Apiquet/STI_Robotic_Competition_Mechanics/AxialBlock.SLDPRT

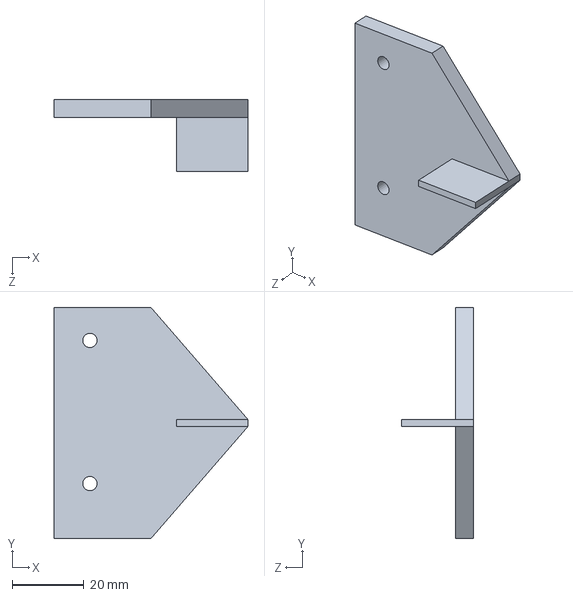
[picture p20: CAD file, 2019-05-12]
AxialBlock.SLDPRT
54.1 x 64.5 x 20.0 mm
