Apiquet/STI_Robotic_Competition_Mechanics/Cam_support/front_cam/Camera_Case.SLDPRT

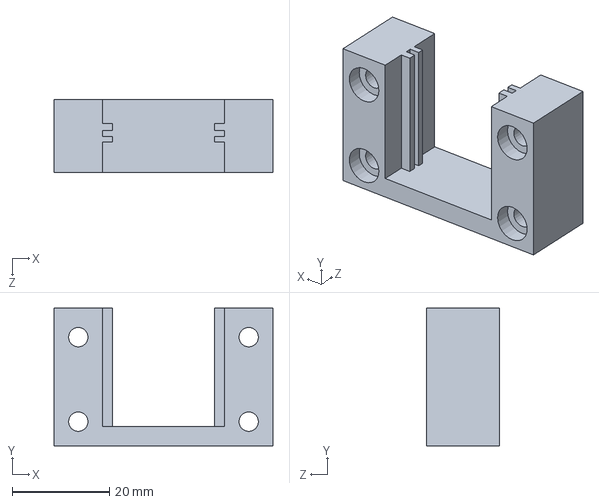
[picture p21: CAD file, 2019-05-05]
Cam_support/front_cam/Camera_Case.SLDPRT
45.1 x 28.4 x 15.0 mm
