Apiquet/STI_Robotic_Competition_Mechanics/Collector_Mechanism/Top_Roller_Holder.SLDPRT

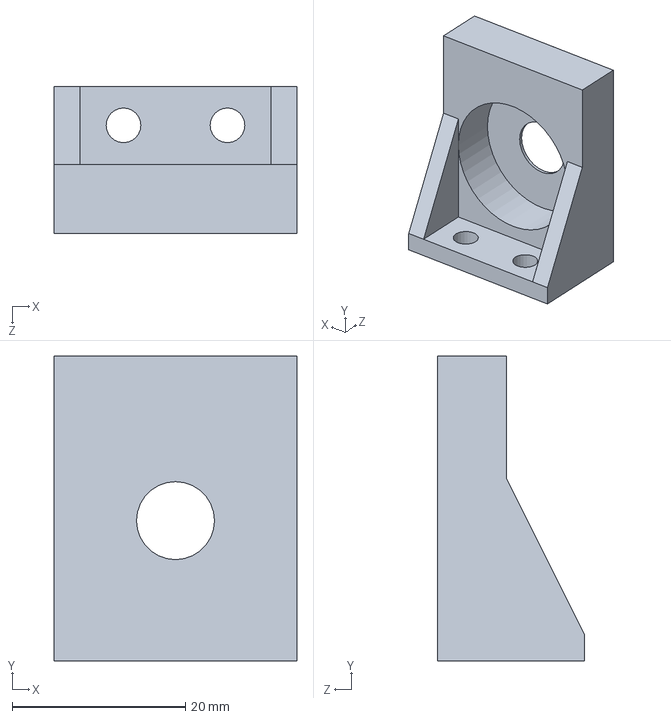
[picture p22: CAD file, 2019-06-13]
Collector_Mechanism/Top_Roller_Holder.SLDPRT
28.0 x 35.2 x 17.0 mm
