Apiquet/STI_Robotic_Competition_Mechanics/Divers/electronics_board/SHARP Sensor.STEP

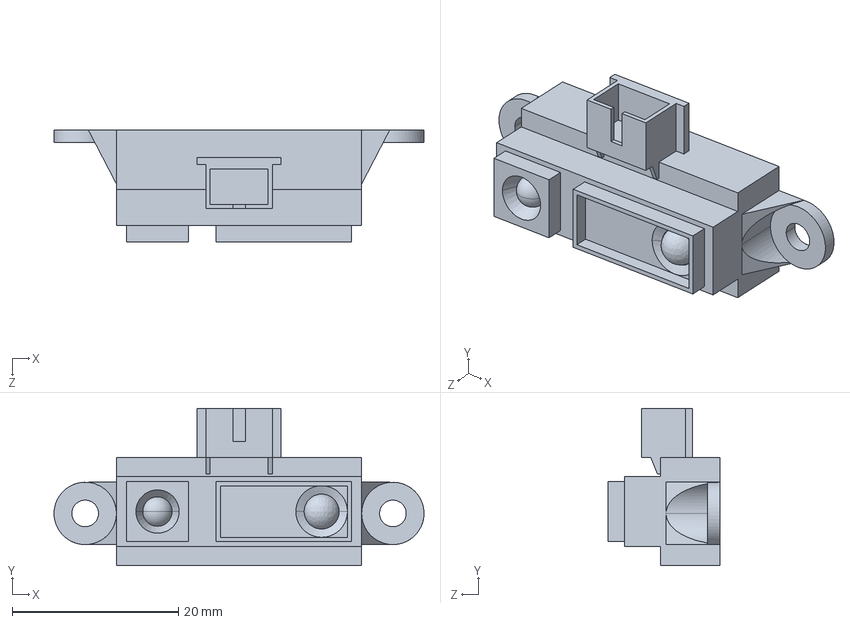
[picture p23: CAD file, 2019-05-03]
Divers/electronics_board/SHARP Sensor.STEP
44.5 x 18.9 x 13.5 mm
