Apiquet/STI_Robotic_Competition_Mechanics/Divers/motors/re25.SLDPRT

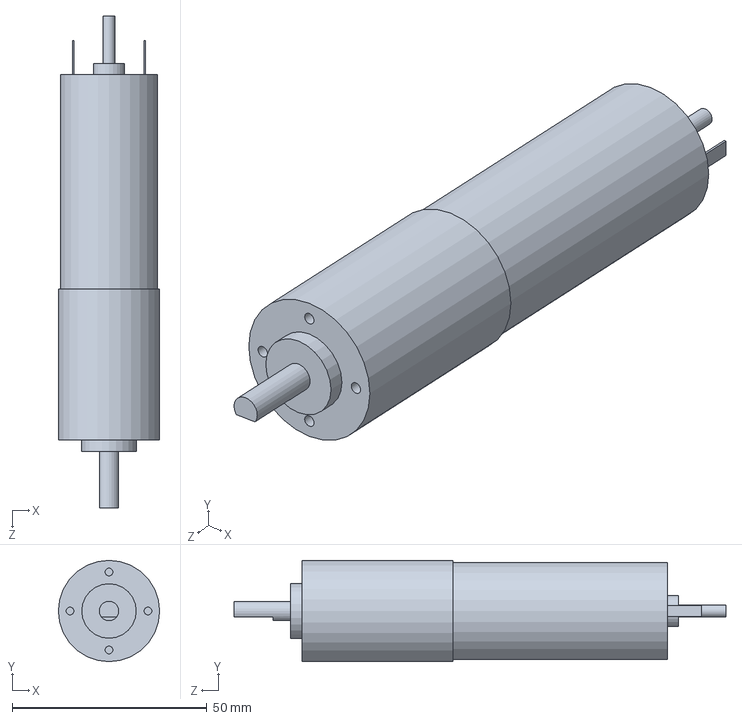
[picture p24: CAD file, 2019-06-13]
Divers/motors/re25.SLDPRT
26.0 x 26.0 x 126.2 mm
