Apiquet/STI_Robotic_Competition_Mechanics/Field/Ramp_True.SLDPRT

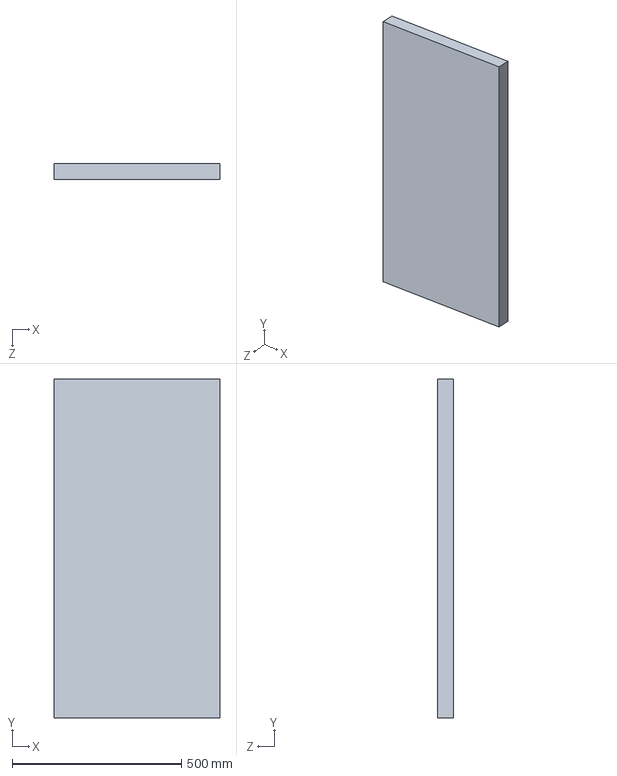
[picture p25: CAD file, 2019-05-09]
Field/Ramp_True.SLDPRT
490.0 x 1001.0 x 47.5 mm
