Apiquet/STI_Robotic_Competition_Mechanics/Prototype_Bottle_Mechanism/high_roller_left_support.SLDPRT

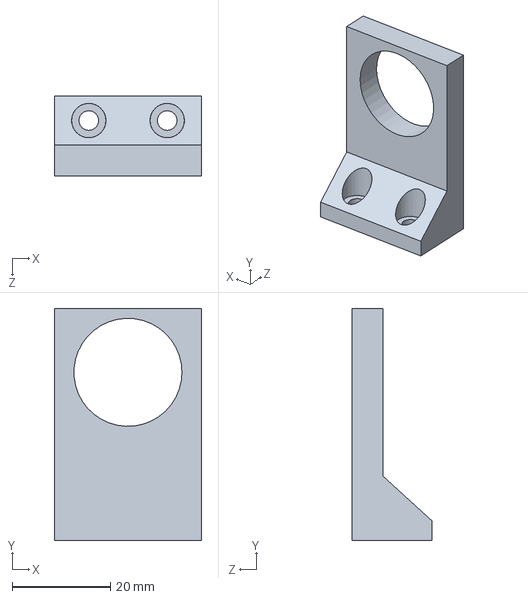
[picture p26: CAD file, 2019-03-28]
Prototype_Bottle_Mechanism/high_roller_left_support.SLDPRT
30.0 x 47.3 x 16.3 mm
