Apiquet/STI_Robotic_Competition_Mechanics/Cam_support/V2/Cone.SLDPRT

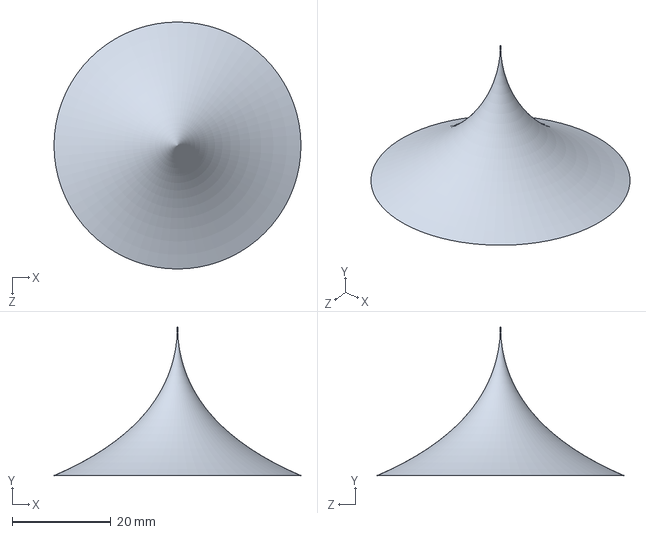
[picture p27: CAD file, 2019-06-13]
Cam_support/V2/Cone.SLDPRT
50.0 x 30.0 x 50.0 mm
