Apiquet/STI_Robotic_Competition_Mechanics/Collector_Mechanism/Bottom_Right_Roller_Holder.SLDPRT

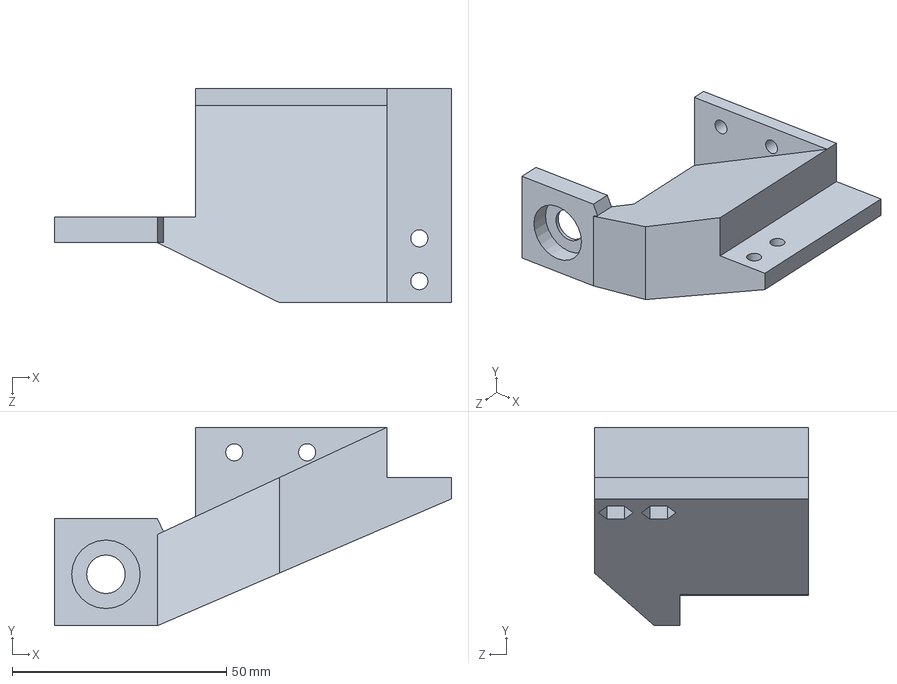
[picture p28: CAD file, 2019-06-13]
Collector_Mechanism/Bottom_Right_Roller_Holder.SLDPRT
92.6 x 46.3 x 50.0 mm
