Apiquet/STI_Robotic_Competition_Mechanics/Divers/electronics_board/DC8-40V_DC12V.SLDPRT

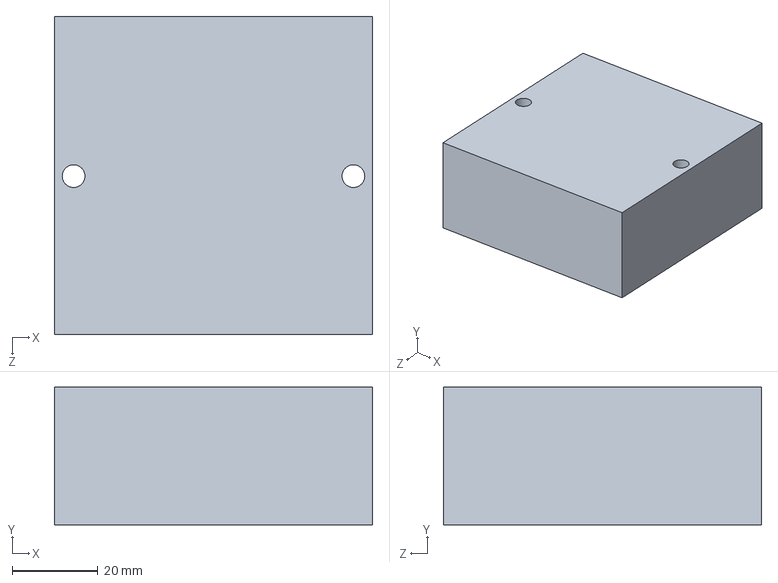
[picture p29: CAD file, 2019-04-24]
Divers/electronics_board/DC8-40V_DC12V.SLDPRT
74.0 x 32.0 x 74.0 mm
