Apiquet/STI_Robotic_Competition_Mechanics/Divers/motors/H38S.SLDPRT

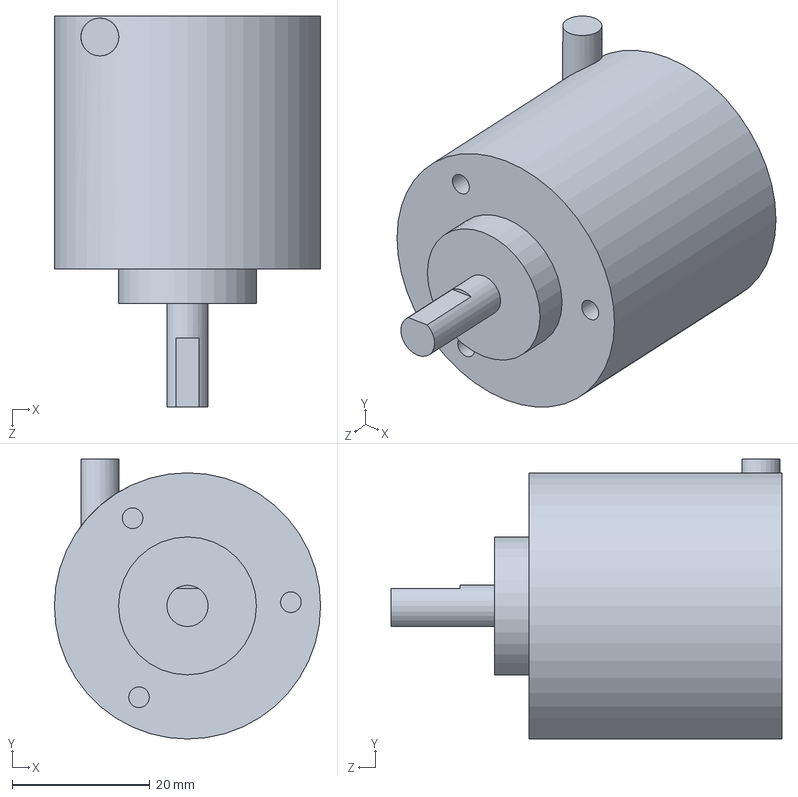
[picture p30: CAD file, 2019-04-23]
Divers/motors/H38S.SLDPRT
38.6 x 40.6 x 56.7 mm
