Apiquet/STI_Robotic_Competition_Mechanics/Divers/Panel_Right.SLDPRT

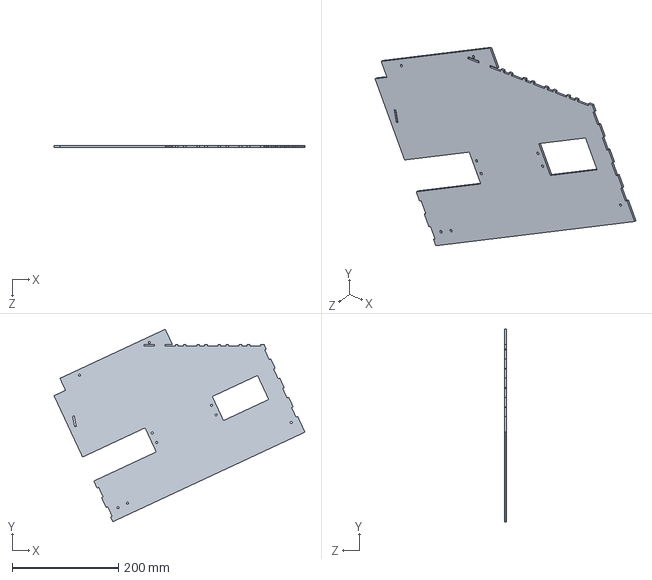
[picture p31: CAD file, 2019-06-15]
Divers/Panel_Right.SLDPRT
473.3 x 363.1 x 3.30 mm
