Apiquet/STI_Robotic_Competition_Mechanics/Drive_Base/Encodeur_Wheel.SLDPRT

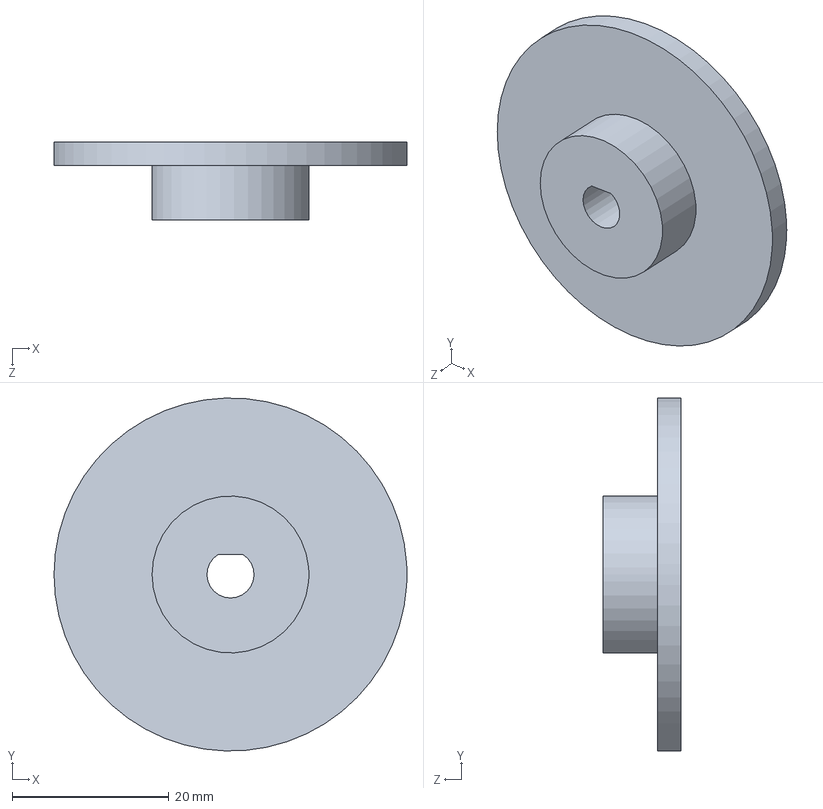
[picture p32: CAD file, 2019-06-13]
Drive_Base/Encodeur_Wheel.SLDPRT
45.0 x 45.0 x 10.0 mm
