Apiquet/STI_Robotic_Competition_Mechanics/Field/Real_Ramp.SLDPRT

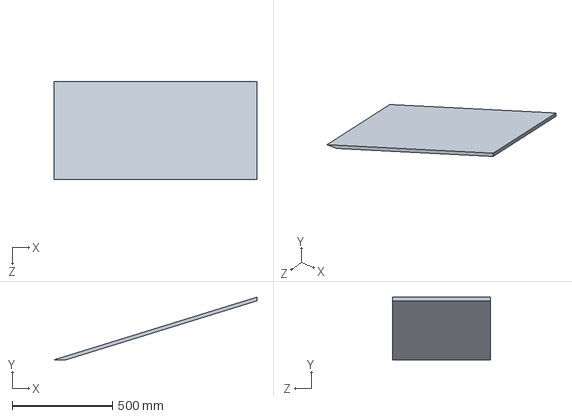
[picture p33: CAD file, 2019-05-09]
Field/Real_Ramp.SLDPRT
1013.0 x 313.0 x 490.0 mm
