Apiquet/STI_Robotic_Competition_Mechanics/Prototype_Bottle_Mechanism/left_motor_support.SLDPRT

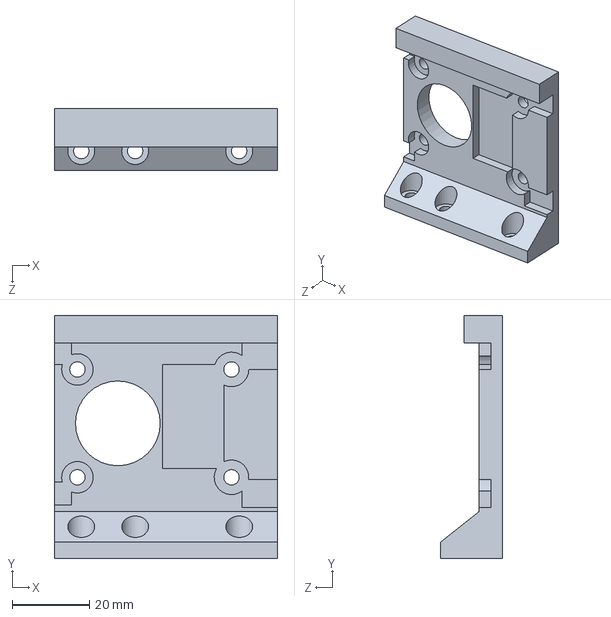
[picture p34: CAD file, 2019-03-28]
Prototype_Bottle_Mechanism/left_motor_support.SLDPRT
58.0 x 63.1 x 16.0 mm
