Apiquet/STI_Robotic_Competition_Mechanics/Sensor/side_sensor_holder.sldprt

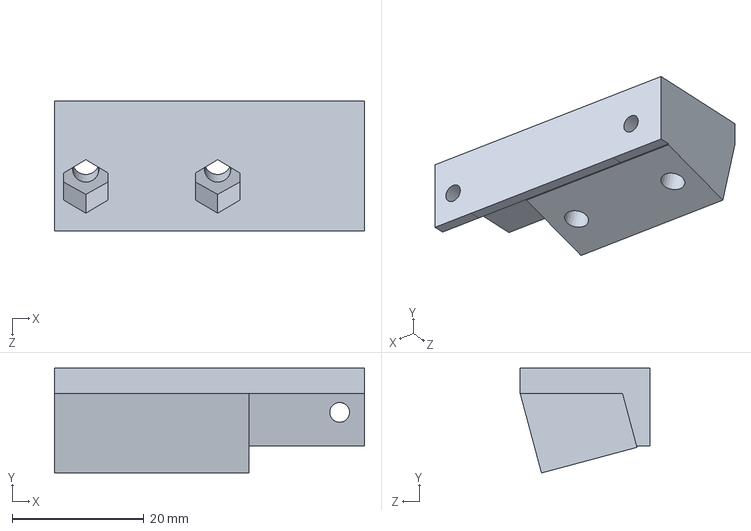
[picture p35: CAD file, 2019-06-13]
Sensor/side_sensor_holder.sldprt
47.0 x 15.9 x 19.7 mm
