Apiquet/STI_Robotic_Competition_Mechanics/Cam_support/V2/Camera_Support.SLDPRT

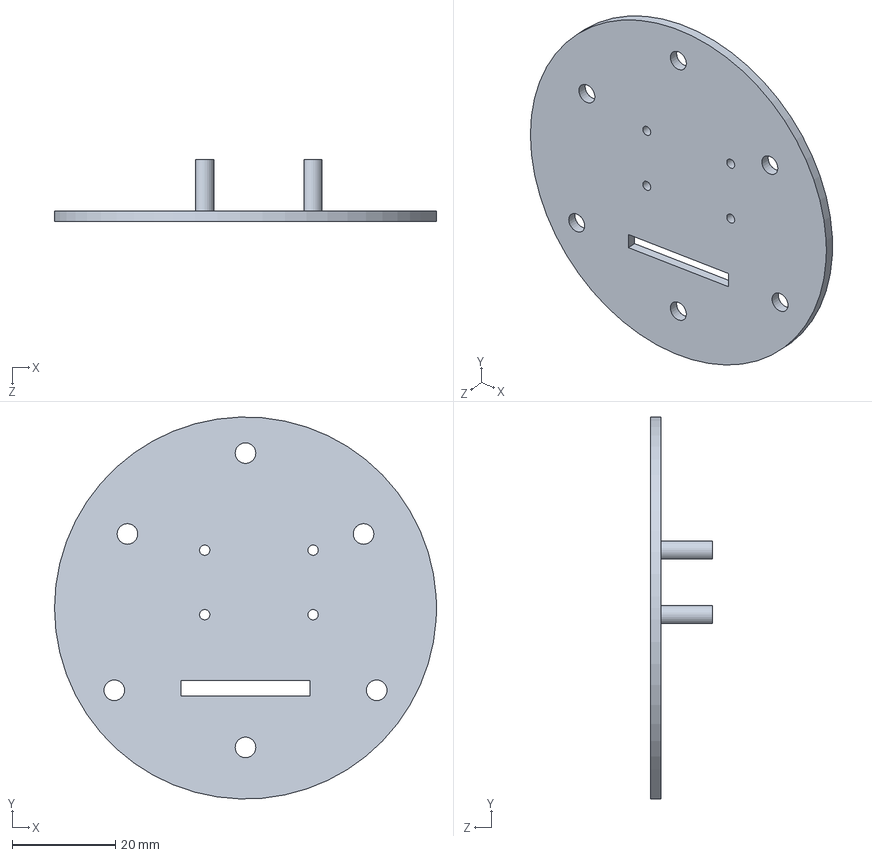
[picture p36: CAD file, 2019-06-13]
Cam_support/V2/Camera_Support.SLDPRT
74.0 x 74.0 x 12.0 mm
