Apiquet/STI_Robotic_Competition_Mechanics/Divers/electronics_board/2x15A_lite.SLDPRT

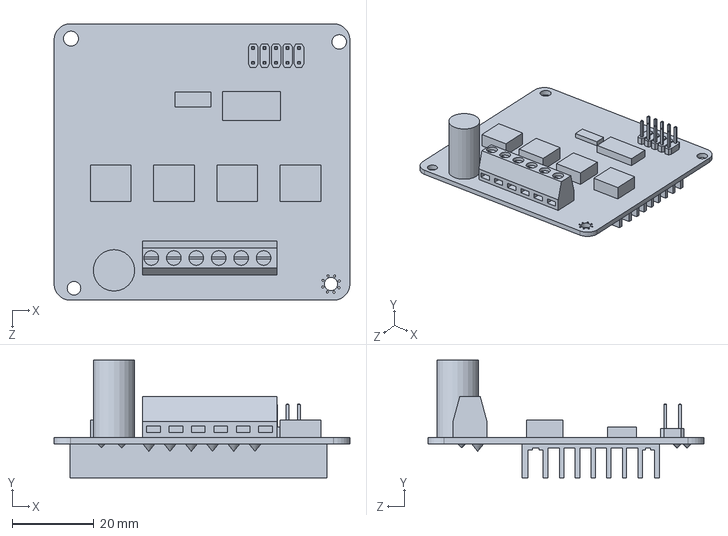
[picture p37: CAD file, 2019-04-24]
Divers/electronics_board/2x15A_lite.SLDPRT
72.5 x 28.9 x 67.7 mm
