Apiquet/STI_Robotic_Competition_Mechanics/Divers/Mirror_Corner_Bearing_Holder.sldprt

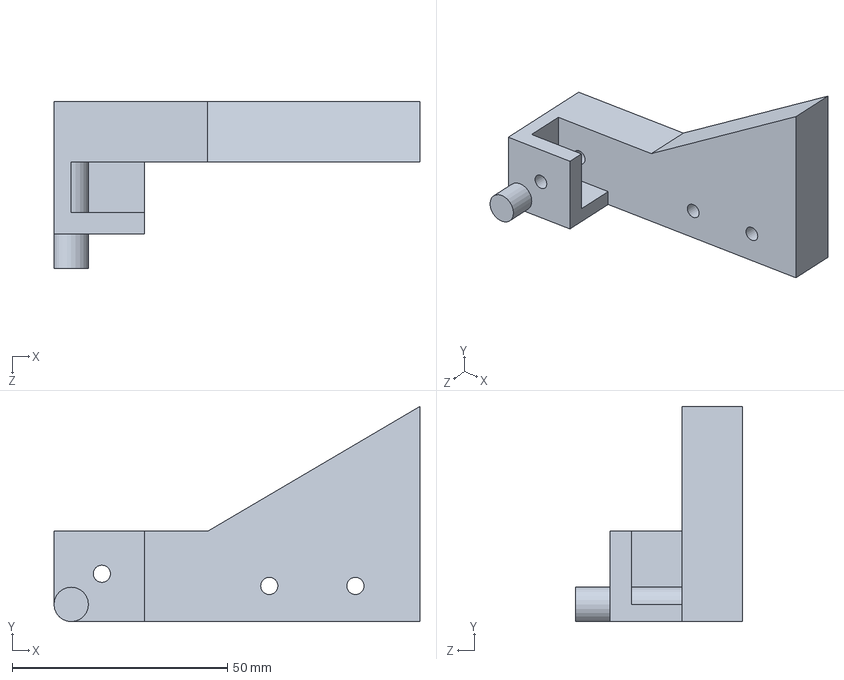
[picture p38: CAD file, 2019-06-13]
Divers/Mirror_Corner_Bearing_Holder.sldprt
85.0 x 50.0 x 38.7 mm
