Apiquet/STI_Robotic_Competition_Mechanics/Field/Obstacle.SLDPRT

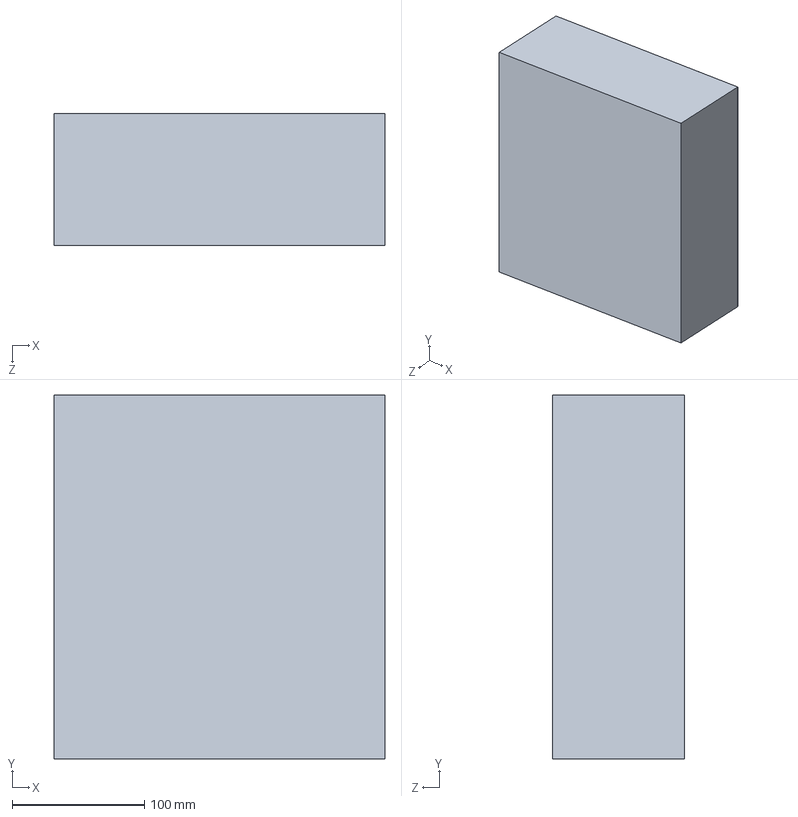
[picture p39: CAD file, 2019-05-03]
Field/Obstacle.SLDPRT
250.0 x 275.0 x 100.0 mm
