Apiquet/STI_Robotic_Competition_Mechanics/Prototype_Bottle_Mechanism/big_motor_supportv2.SLDPRT

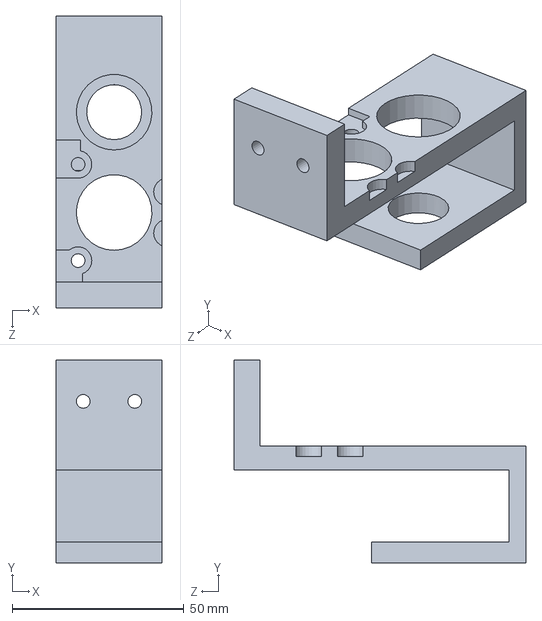
[picture p40: CAD file, 2019-03-20]
Prototype_Bottle_Mechanism/big_motor_supportv2.SLDPRT
31.0 x 59.0 x 85.0 mm
