Apiquet/STI_Robotic_Competition_Mechanics/Sensor/Sensor_Side_Back_V2.sldprt

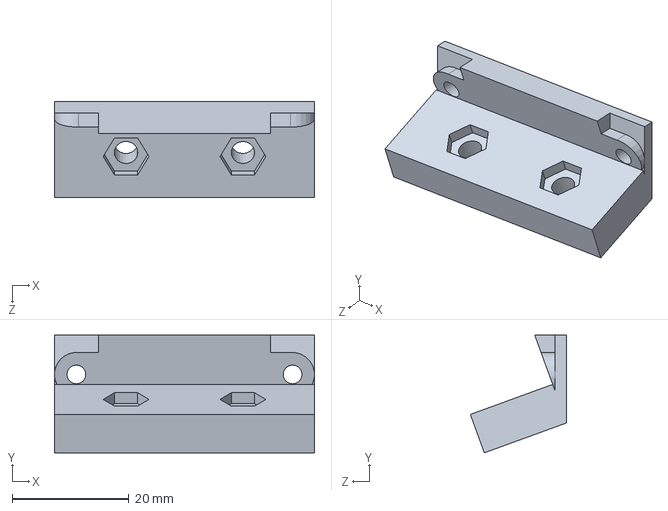
[picture p41: CAD file, 2019-05-20]
Sensor/Sensor_Side_Back_V2.sldprt
44.5 x 20.1 x 16.5 mm
