Apiquet/STI_Robotic_Competition_Mechanics/Cam_support/V2/base_cam_support.SLDPRT

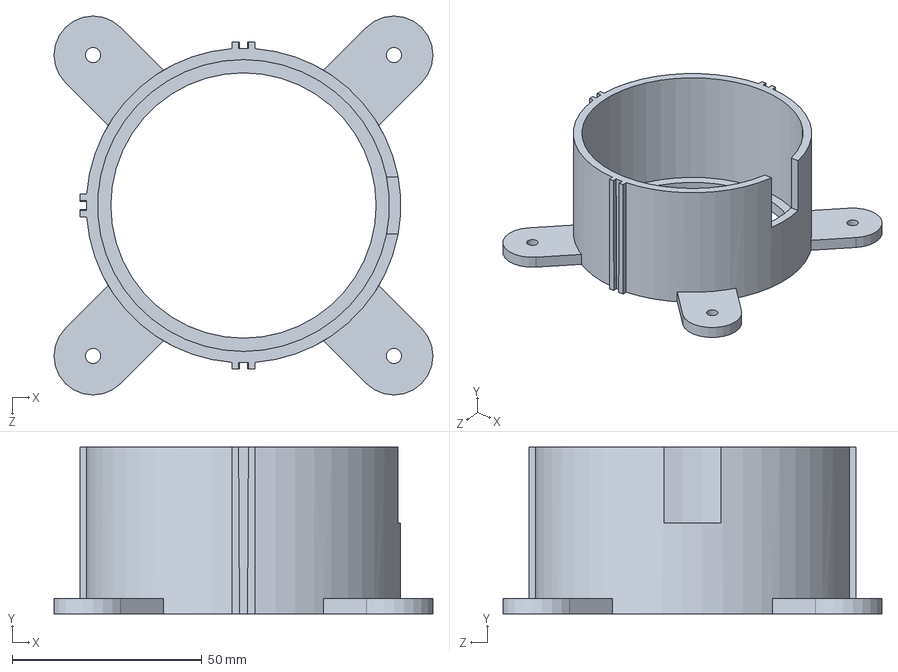
[picture p42: CAD file, 2019-06-13]
Cam_support/V2/base_cam_support.SLDPRT
100.0 x 44.0 x 100.0 mm
