Apiquet/STI_Robotic_Competition_Mechanics/Collector_Mechanism/Back_Motor_Roller_Support.SLDPRT

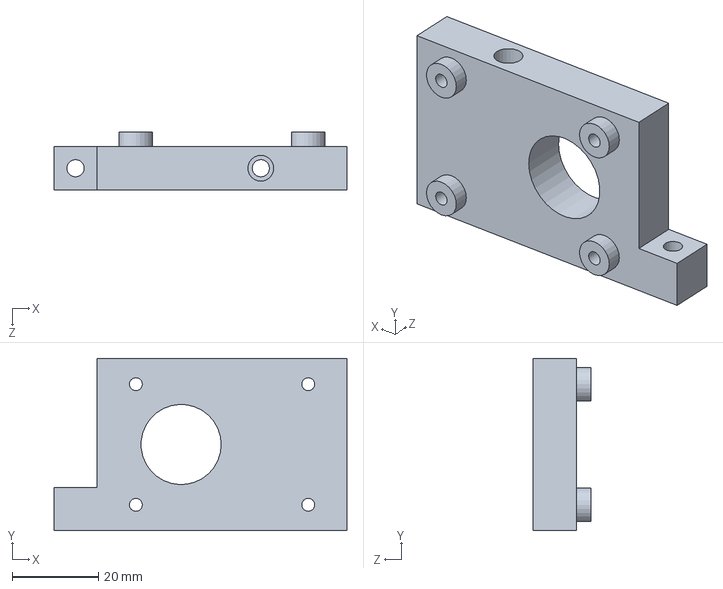
[picture p43: CAD file, 2019-05-30]
Collector_Mechanism/Back_Motor_Roller_Support.SLDPRT
68.0 x 40.0 x 13.4 mm
