Apiquet/STI_Robotic_Competition_Mechanics/Divers/electronics_board/powerboard_robopoly.SLDPRT

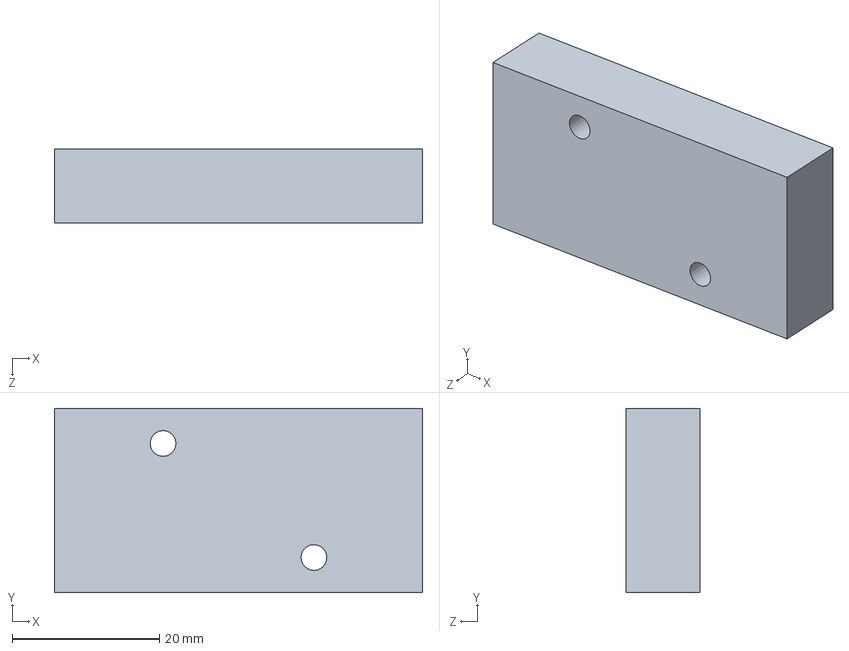
[picture p44: CAD file, 2019-03-14]
Divers/electronics_board/powerboard_robopoly.SLDPRT
50.0 x 25.0 x 10.0 mm
