Apiquet/STI_Robotic_Competition_Mechanics/Divers/Panel_Roof.SLDPRT

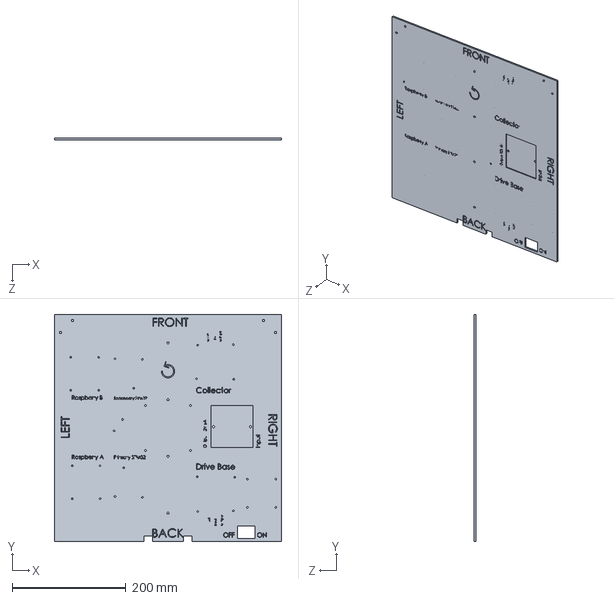
[picture p45: CAD file, 2019-06-13]
Divers/Panel_Roof.SLDPRT
400.0 x 400.0 x 3.30 mm
