Apiquet/STI_Robotic_Competition_Mechanics/Prototype_Bottle_Mechanism/wedge_left_side.SLDPRT

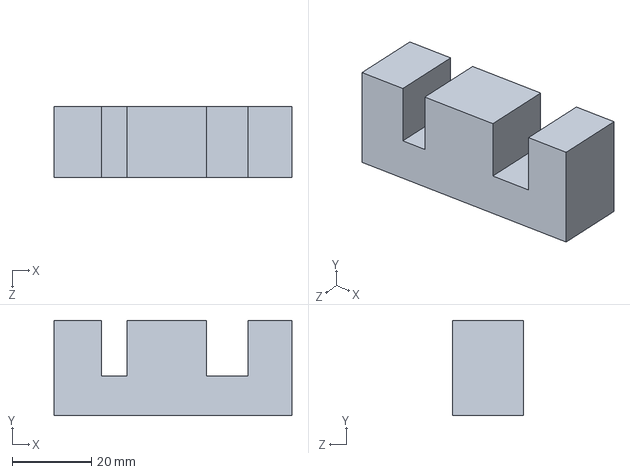
[picture p46: CAD file, 2019-03-18]
Prototype_Bottle_Mechanism/wedge_left_side.SLDPRT
60.0 x 24.0 x 18.0 mm
