Apiquet/STI_Robotic_Competition_Mechanics/Sensor/Front_Sensor_holder.SLDPRT

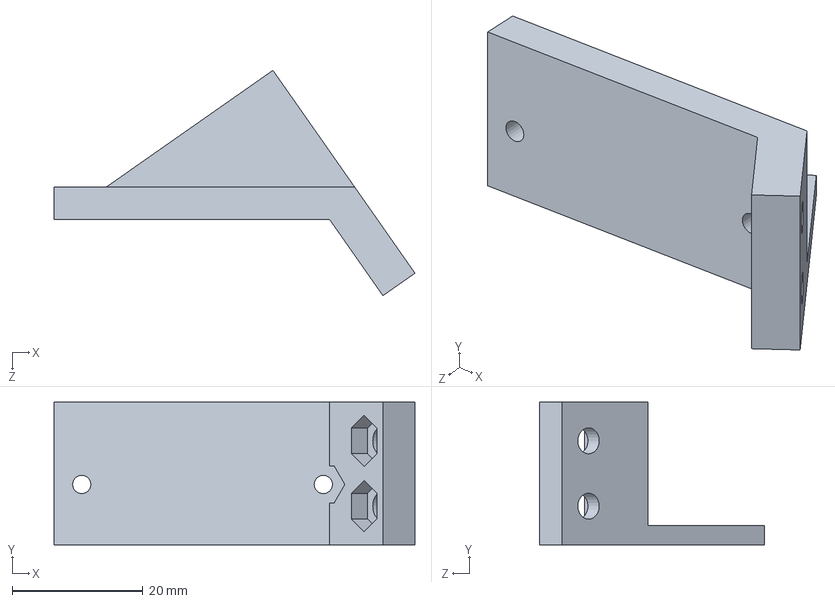
[picture p47: CAD file, 2019-05-14]
Sensor/Front_Sensor_holder.SLDPRT
55.3 x 21.9 x 34.5 mm
