Apiquet/STI_Robotic_Competition_Mechanics/Collector_Mechanism/Top_Motor_Holder.SLDPRT

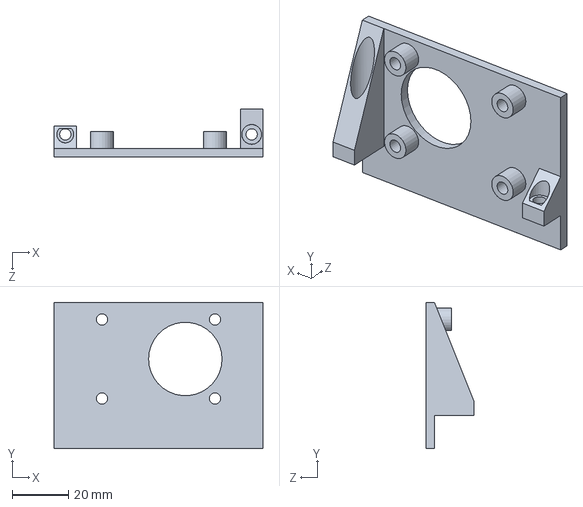
[picture p48: CAD file, 2019-05-30]
Collector_Mechanism/Top_Motor_Holder.SLDPRT
74.0 x 51.7 x 17.0 mm
