Apiquet/STI_Robotic_Competition_Mechanics/Divers/electronics_board/MDD10A_REV2.0.SLDPRT

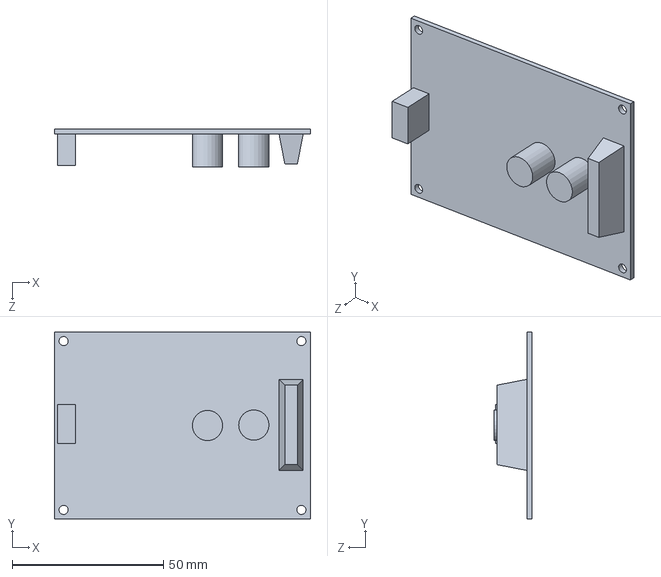
[picture p49: CAD file, 2019-03-14]
Divers/electronics_board/MDD10A_REV2.0.SLDPRT
84.5 x 61.7 x 12.7 mm
