Apiquet/STI_Robotic_Competition_Mechanics/Divers/motors/motor_roller.SLDPRT

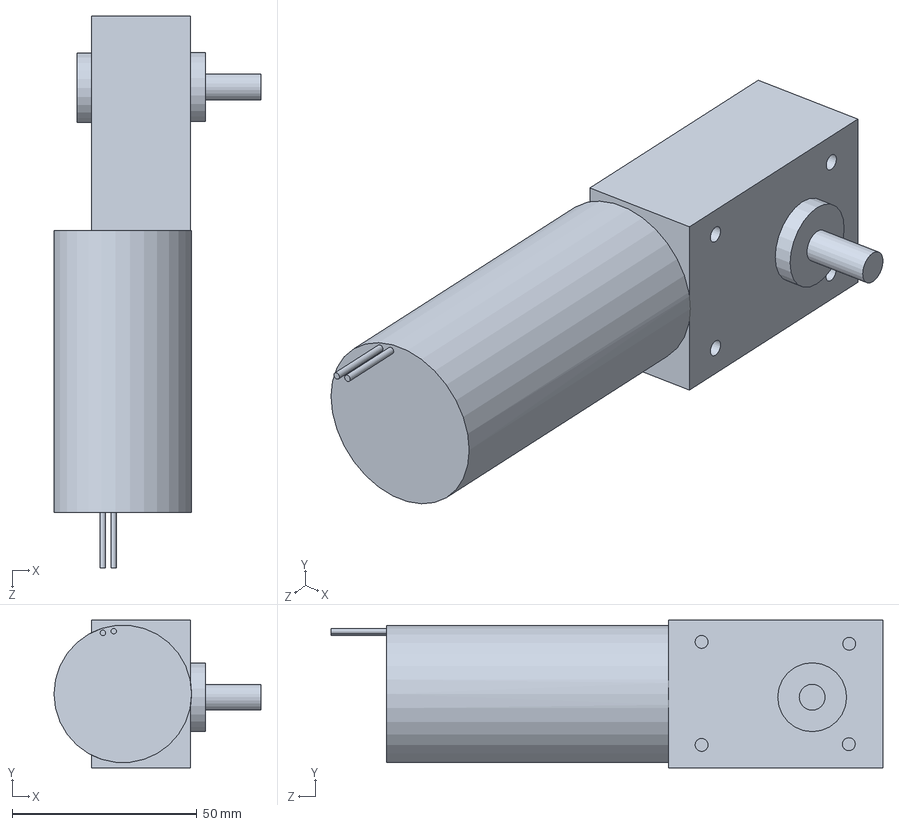
[picture p50: CAD file, 2019-03-17]
Divers/motors/motor_roller.SLDPRT
56.0 x 40.0 x 149.2 mm
