Apiquet/STI_Robotic_Competition_Mechanics/Drive_Base/Axial_Blocker.SLDPRT

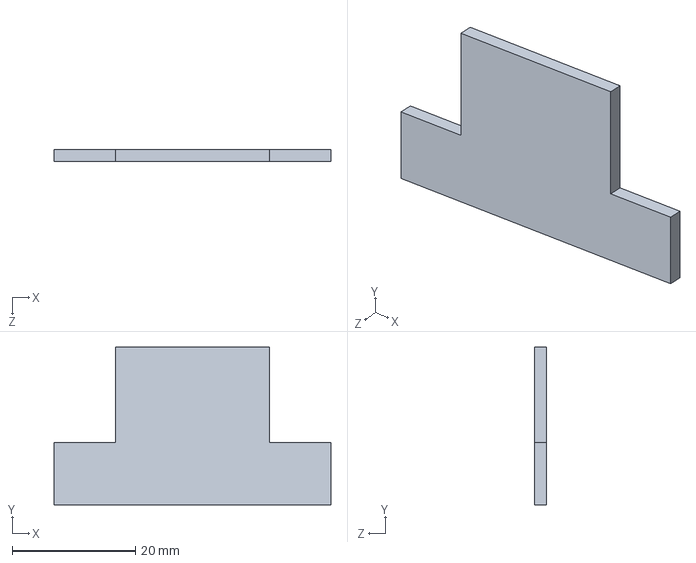
[picture p51: CAD file, 2019-06-13]
Drive_Base/Axial_Blocker.SLDPRT
45.0 x 25.6 x 2.00 mm
