Apiquet/STI_Robotic_Competition_Mechanics/Field/Ramp_Field.SLDPRT

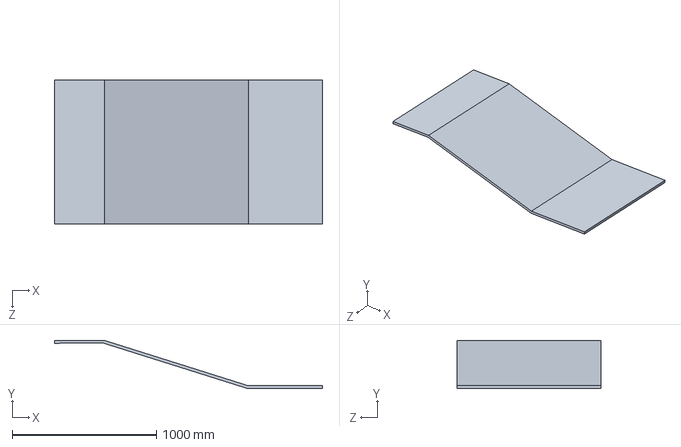
[picture p52: CAD file, 2019-04-21]
Field/Ramp_Field.SLDPRT
1855.6 x 334.1 x 1000.0 mm
