Apiquet/STI_Robotic_Competition_Mechanics/Prototype_Bottle_Mechanism/Bearing22_9.9_6mm - Copy.SLDPRT

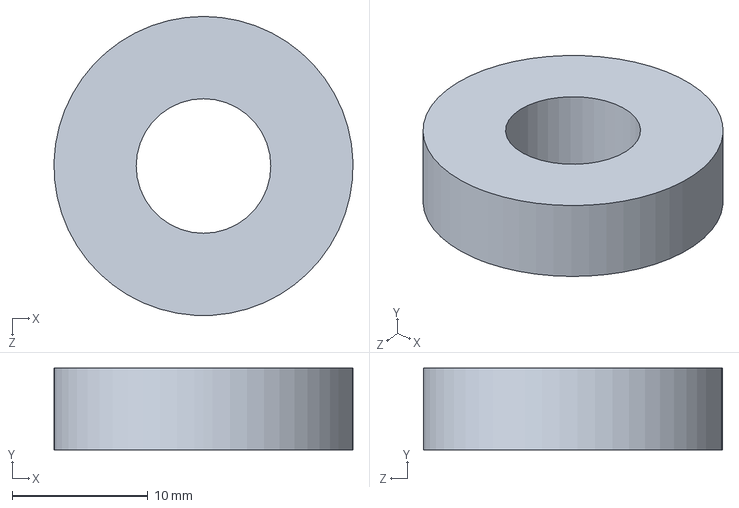
[picture p53: CAD file, 2019-03-18]
Prototype_Bottle_Mechanism/Bearing22_9.9_6mm - Copy.SLDPRT
22.0 x 6.00 x 22.0 mm
