Apiquet/STI_Robotic_Competition_Mechanics/Sensor/Front_Middle_Sensor_Holder.SLDPRT

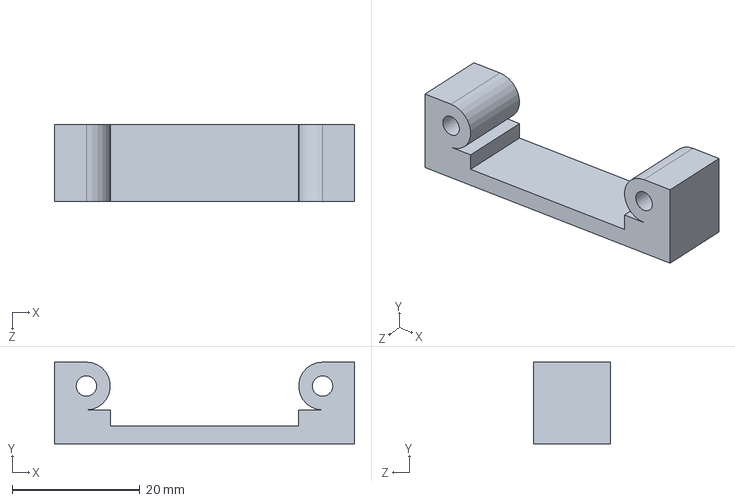
[picture p54: CAD file, 2019-05-14]
Sensor/Front_Middle_Sensor_Holder.SLDPRT
47.0 x 12.8 x 12.0 mm
