Apiquet/STI_Robotic_Competition_Mechanics/Cam_support/V2/glass.SLDPRT

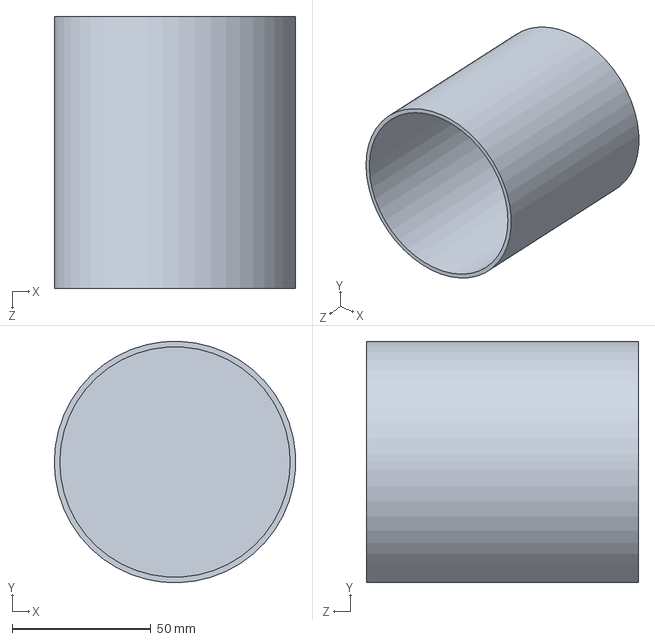
[picture p55: CAD file, 2019-06-13]
Cam_support/V2/glass.SLDPRT
87.0 x 87.0 x 98.0 mm
