Apiquet/STI_Robotic_Competition_Mechanics/Collector_Mechanism/Wooden_Ramp.SLDPRT

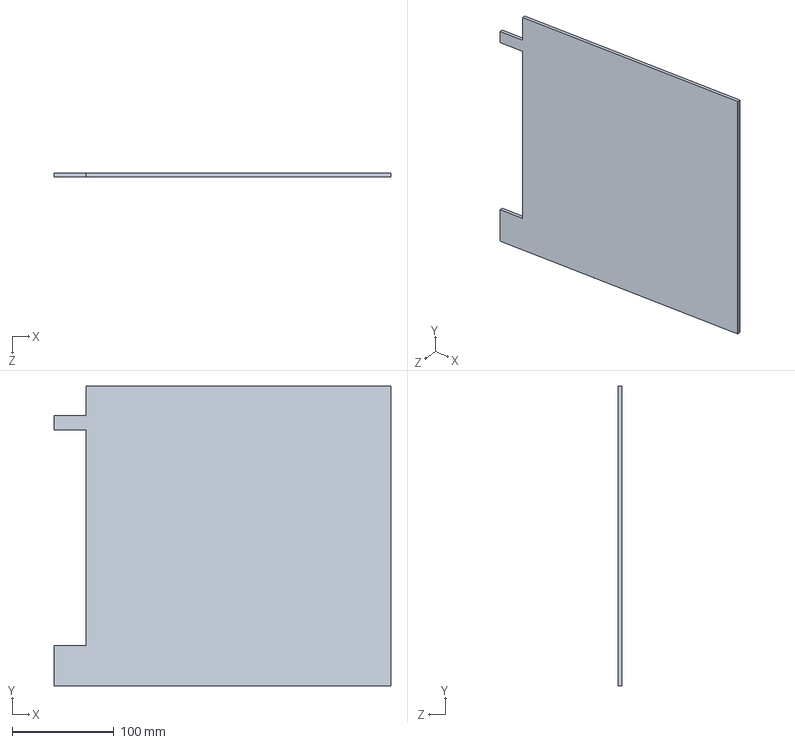
[picture p56: CAD file, 2019-05-20]
Collector_Mechanism/Wooden_Ramp.SLDPRT
331.5 x 295.0 x 4.00 mm
