Apiquet/STI_Robotic_Competition_Mechanics/Divers/motors/GM37.SLDPRT

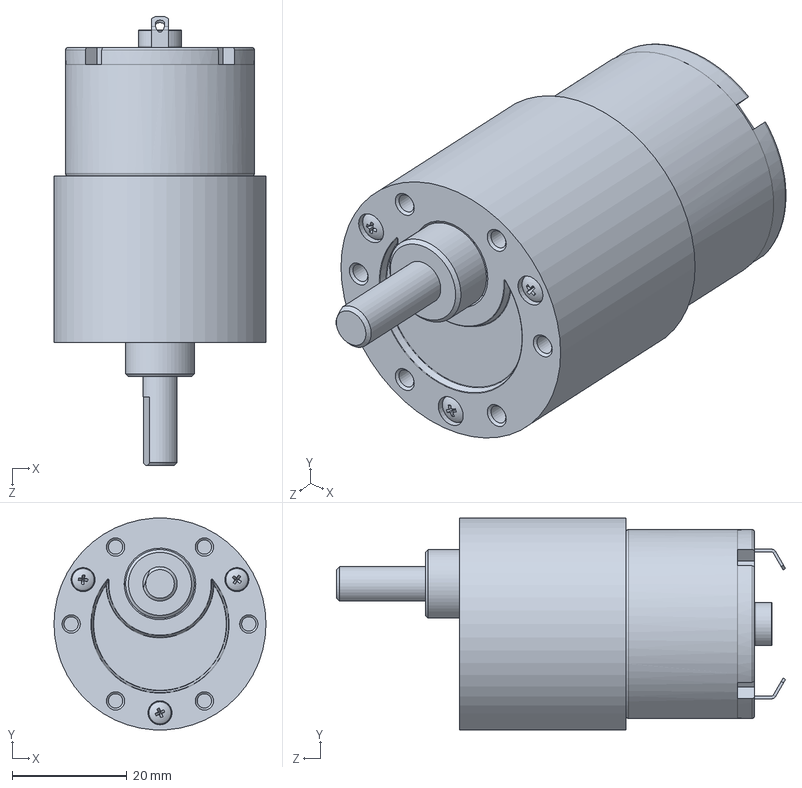
[picture p57: CAD file, 2019-03-14]
Divers/motors/GM37.SLDPRT
37.0 x 36.9 x 78.4 mm
