Apiquet/STI_Robotic_Competition_Mechanics/Prototype_Bottle_Mechanism/roller_holder_v2_left.SLDPRT

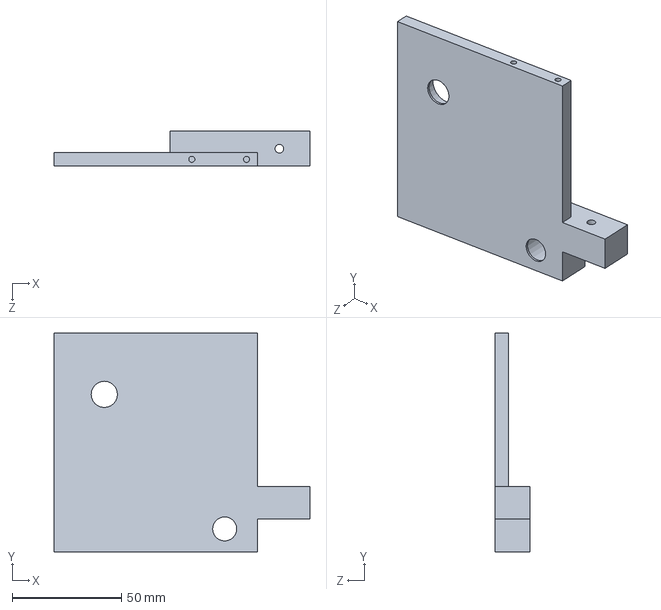
[picture p58: CAD file, 2019-03-18]
Prototype_Bottle_Mechanism/roller_holder_v2_left.SLDPRT
117.0 x 100.0 x 16.2 mm
