Apiquet/STI_Robotic_Competition_Mechanics/Sensor/Front_side_sensor_holder.sldprt

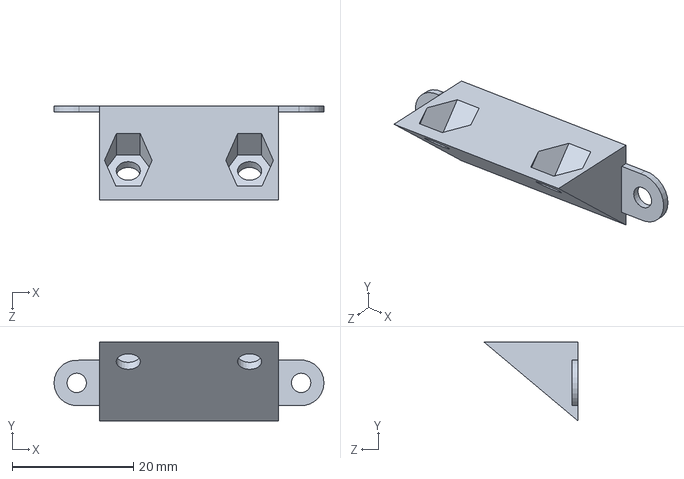
[picture p59: CAD file, 2019-05-14]
Sensor/Front_side_sensor_holder.sldprt
44.5 x 13.0 x 15.5 mm
