Apiquet/STI_Robotic_Competition_Mechanics/Cam_support/V2/Camera_Case.SLDPRT

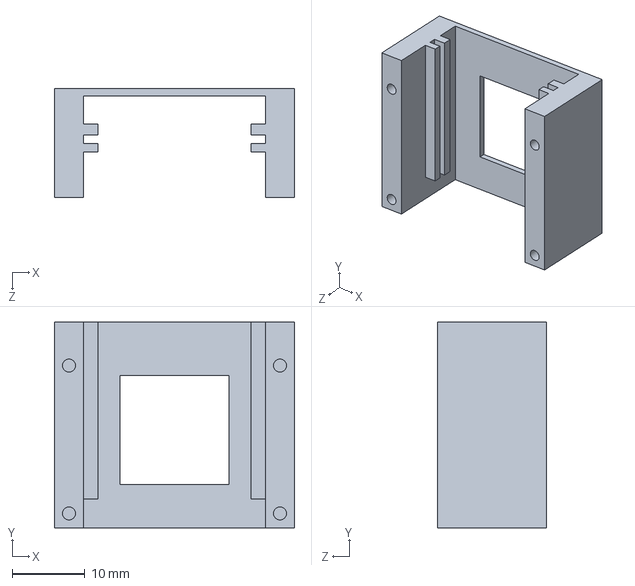
[picture p60: CAD file, 2019-03-21]
Cam_support/V2/Camera_Case.SLDPRT
33.1 x 28.4 x 15.0 mm
