Apiquet/STI_Robotic_Competition_Mechanics/Collector_Mechanism/Bottom_Left_Roller_Holder.SLDPRT

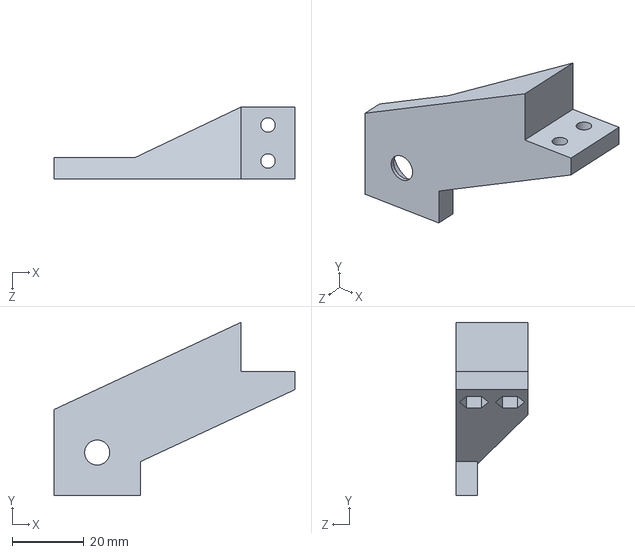
[picture p61: CAD file, 2019-05-20]
Collector_Mechanism/Bottom_Left_Roller_Holder.SLDPRT
67.0 x 48.2 x 20.0 mm
