Apiquet/STI_Robotic_Competition_Mechanics/Drive_Base/Axial_Encoder_Holder.SLDPRT

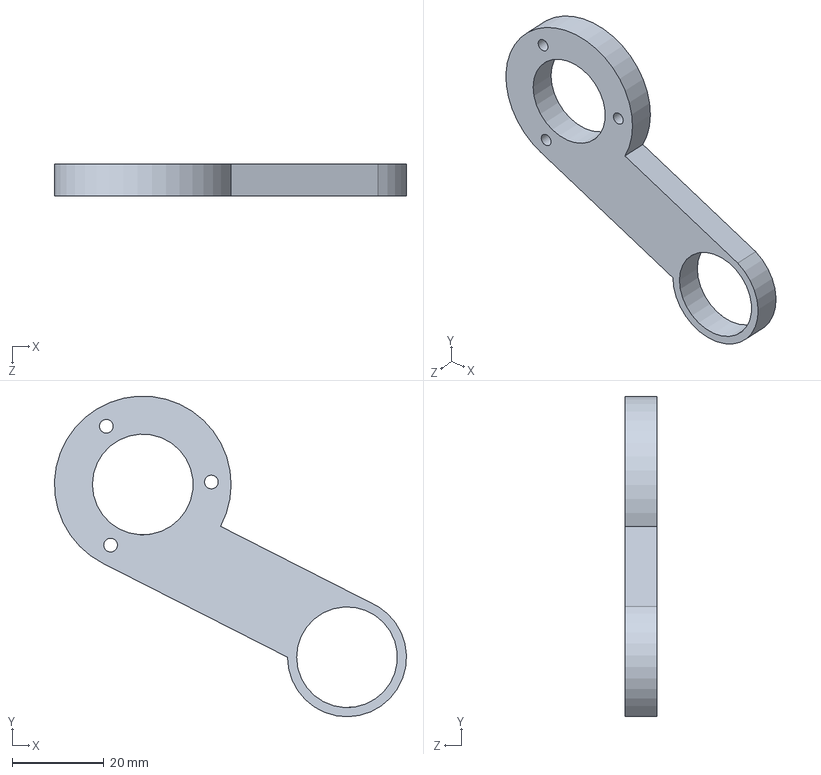
[picture p62: CAD file, 2019-06-13]
Drive_Base/Axial_Encoder_Holder.SLDPRT
76.9 x 70.0 x 7.00 mm
