Apiquet/STI_Robotic_Competition_Mechanics/Prototype_Bottle_Mechanism/10mmAxis_then_8mm.SLDPRT

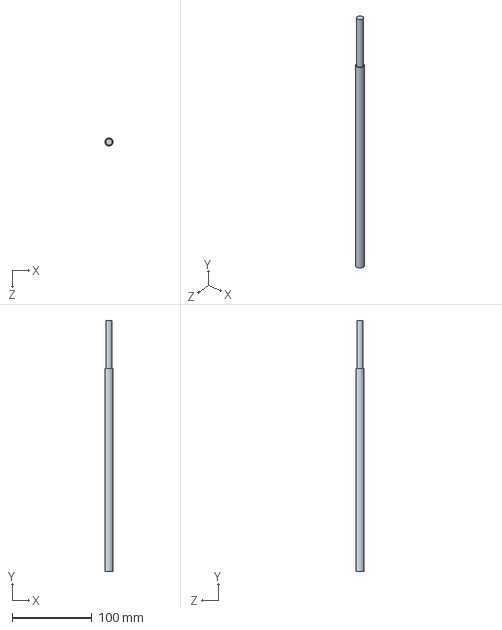
[picture p63: CAD file, 2019-03-18]
Prototype_Bottle_Mechanism/10mmAxis_then_8mm.SLDPRT
10.0 x 314.0 x 10.0 mm
