Apiquet/STI_Robotic_Competition_Mechanics/Cam_support/V2/mount_glass.SLDPRT

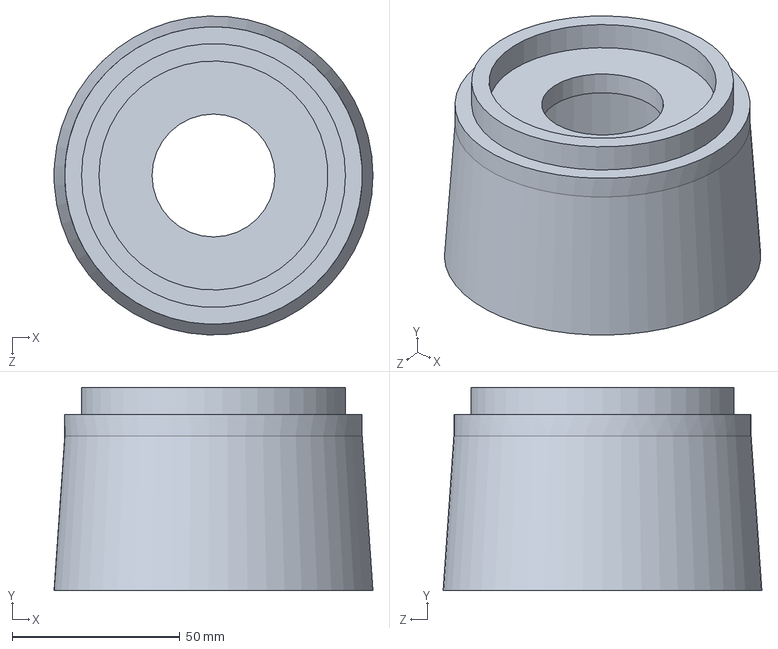
[picture p64: CAD file, 2019-03-20]
Cam_support/V2/mount_glass.SLDPRT
95.0 x 60.5 x 95.0 mm
