Apiquet/STI_Robotic_Competition_Mechanics/Collector_Mechanism/pinion_gear.sldprt

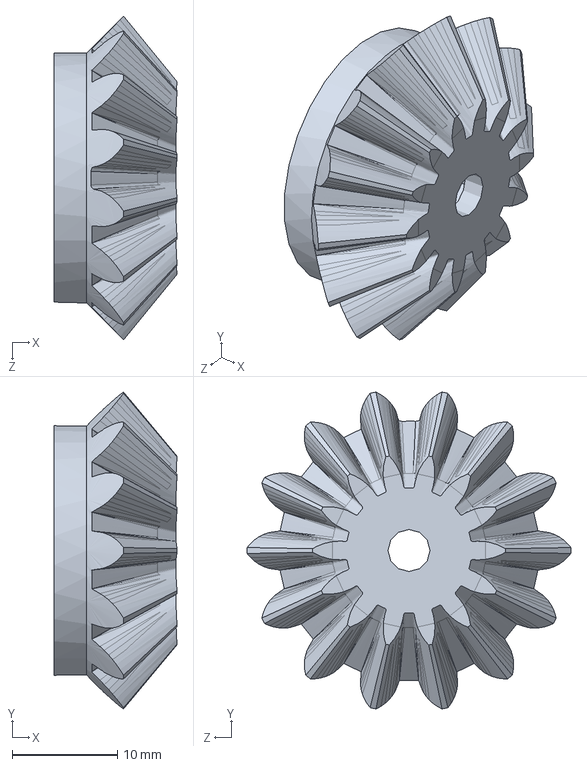
[picture p65: CAD file, 2019-05-09]
Collector_Mechanism/pinion_gear.sldprt
11.7 x 30.2 x 30.8 mm
