Apiquet/STI_Robotic_Competition_Mechanics/Divers/Corner_Bearing_Holder_Small.sldprt

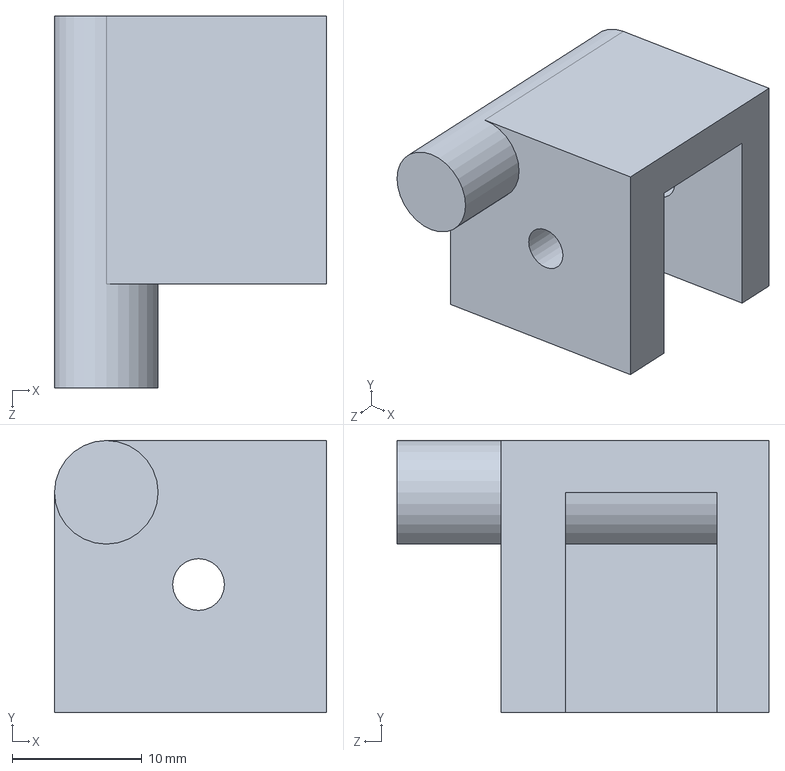
[picture p66: CAD file, 2019-06-13]
Divers/Corner_Bearing_Holder_Small.sldprt
21.0 x 21.0 x 28.7 mm
