Apiquet/STI_Robotic_Competition_Mechanics/Drive_Base/Axis_Encodeur_Holder.SLDPRT

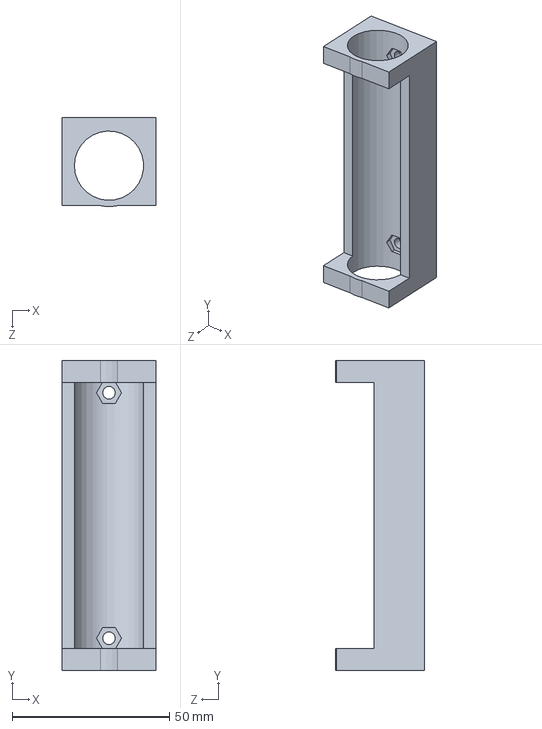
[picture p67: CAD file, 2019-05-30]
Drive_Base/Axis_Encodeur_Holder.SLDPRT
30.0 x 98.5 x 28.3 mm
