Apiquet/STI_Robotic_Competition_Mechanics/Prototype_Bottle_Mechanism/AdapterhubHex.SLDPRT

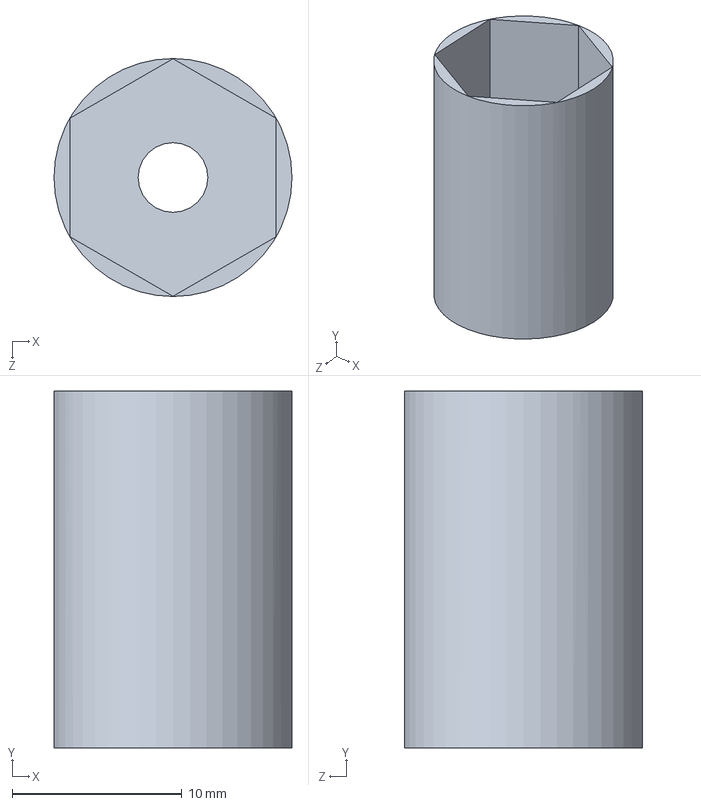
[picture p68: CAD file, 2019-03-18]
Prototype_Bottle_Mechanism/AdapterhubHex.SLDPRT
14.0 x 21.0 x 14.0 mm
