Apiquet/STI_Robotic_Competition_Mechanics/Sensor/Back_Side_Sensor_Holder.SLDPRT

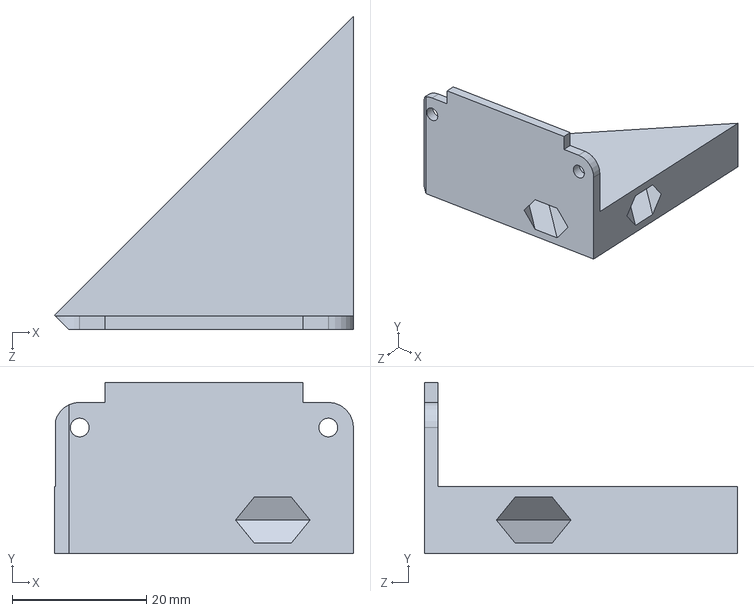
[picture p69: CAD file, 2019-05-03]
Sensor/Back_Side_Sensor_Holder.SLDPRT
44.5 x 25.5 x 46.6 mm
