Apiquet/STI_Robotic_Competition_Mechanics/Cam_support/V2/joint.SLDPRT

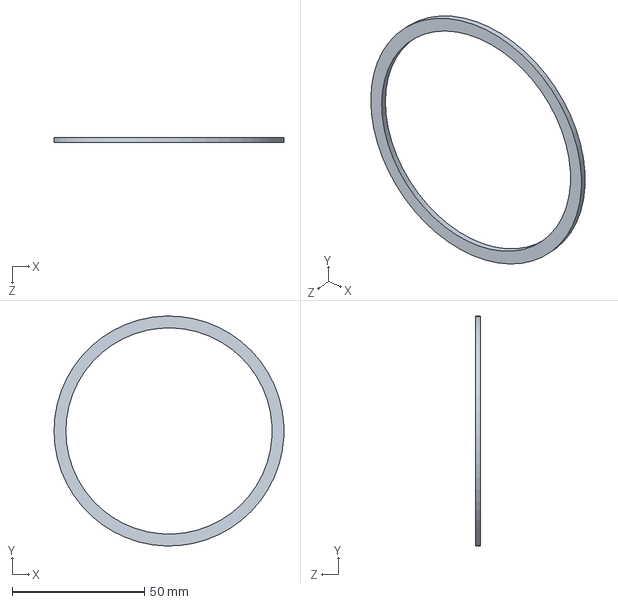
[picture p70: CAD file, 2019-03-20]
Cam_support/V2/joint.SLDPRT
87.0 x 87.0 x 2.00 mm
