Apiquet/STI_Robotic_Competition_Mechanics/Divers/Panel_Bottom_Right_Side.SLDPRT

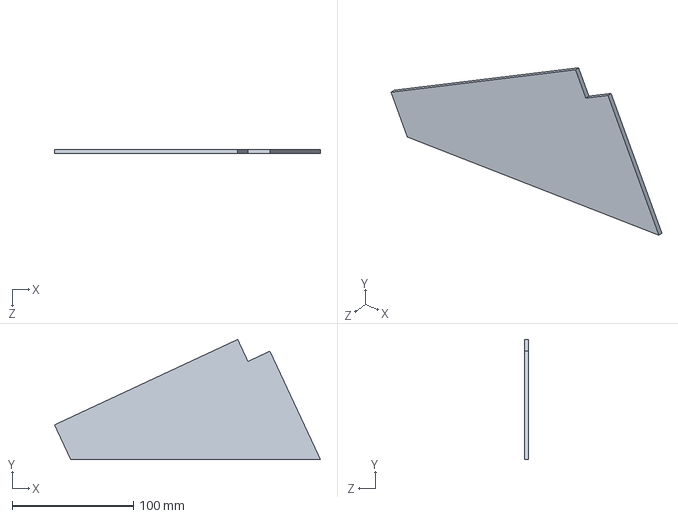
[picture p71: CAD file, 2019-05-30]
Divers/Panel_Bottom_Right_Side.SLDPRT
219.3 x 99.0 x 3.30 mm
