Apiquet/STI_Robotic_Competition_Mechanics/Drive_Base/Support_Encoder_springy.SLDPRT

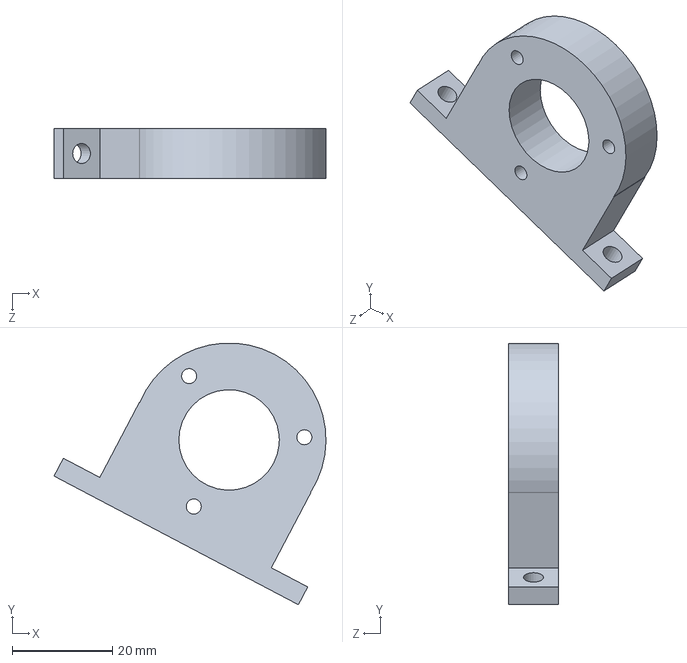
[picture p72: CAD file, 2019-05-12]
Drive_Base/Support_Encoder_springy.SLDPRT
54.2 x 52.1 x 10.0 mm
