Apiquet/STI_Robotic_Competition_Mechanics/Prototype_Bottle_Mechanism/Foam_v2_10mmAxis.SLDPRT

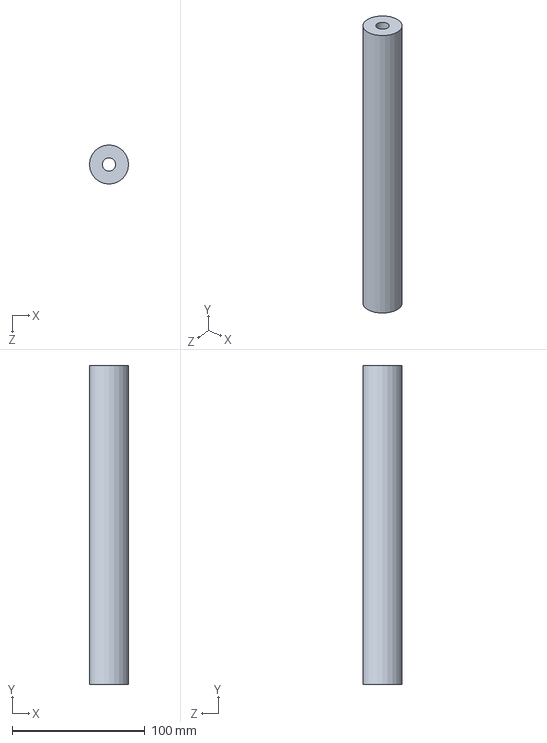
[picture p73: CAD file, 2019-03-18]
Prototype_Bottle_Mechanism/Foam_v2_10mmAxis.SLDPRT
29.4 x 240.0 x 29.4 mm
