Apiquet/STI_Robotic_Competition_Mechanics/Collector_Mechanism/Roller_Bottom.SLDPRT

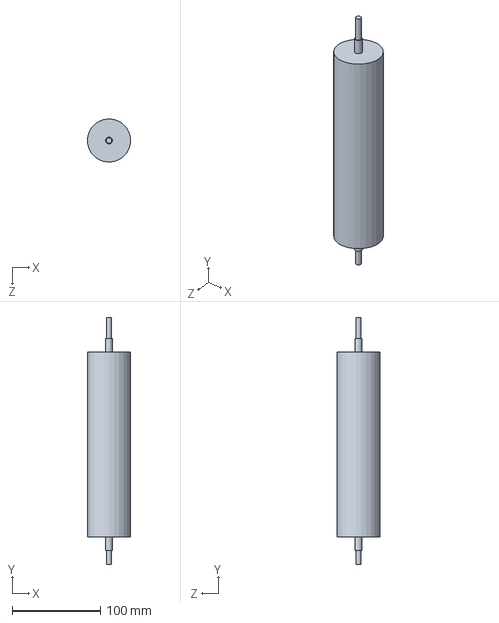
[picture p74: CAD file, 2019-05-05]
Collector_Mechanism/Roller_Bottom.SLDPRT
48.6 x 280.0 x 49.0 mm
