Apiquet/STI_Robotic_Competition_Mechanics/Divers/Panel_Left.SLDPRT

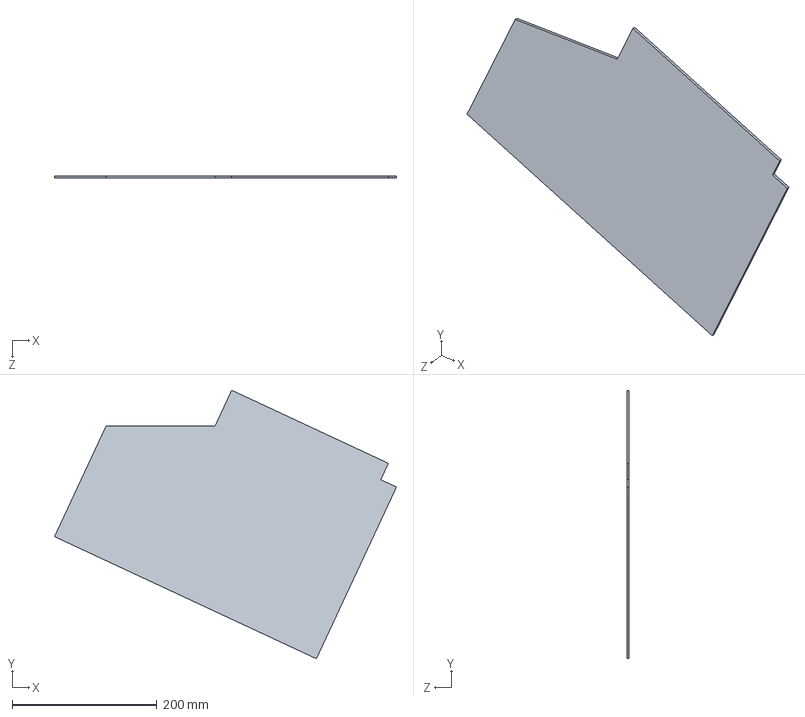
[picture p75: CAD file, 2019-05-30]
Divers/Panel_Left.SLDPRT
473.3 x 371.6 x 3.30 mm
