Apiquet/STI_Robotic_Competition_Mechanics/Drive_Base/Mask_Drill_springy_encodeur.SLDPRT

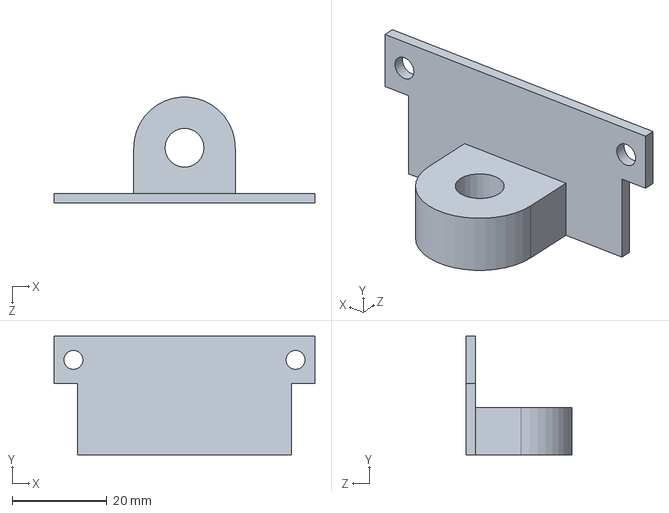
[picture p76: CAD file, 2019-05-12]
Drive_Base/Mask_Drill_springy_encodeur.SLDPRT
55.0 x 25.0 x 22.3 mm
