Apiquet/STI_Robotic_Competition_Mechanics/Collector_Mechanism/Gear_Sprocket_Fusion.SLDPRT

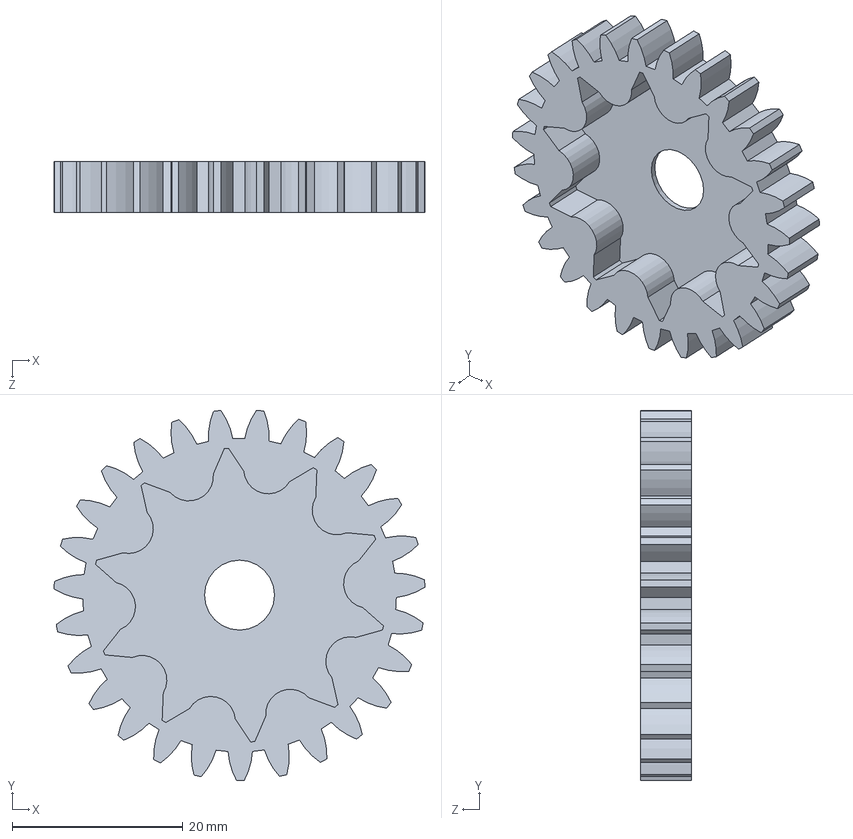
[picture p77: CAD file, 2019-04-24]
Collector_Mechanism/Gear_Sprocket_Fusion.SLDPRT
43.5 x 43.4 x 6.00 mm
