Apiquet/STI_Robotic_Competition_Mechanics/Divers/Panel_Back.SLDPRT

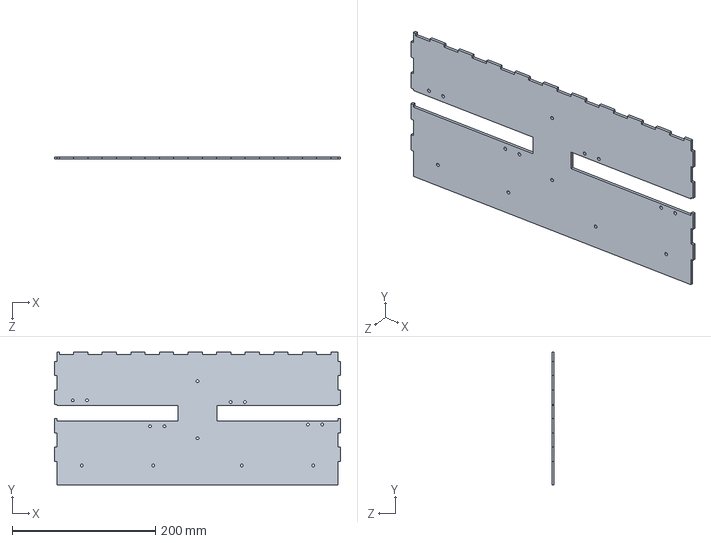
[picture p78: CAD file, 2019-05-30]
Divers/Panel_Back.SLDPRT
400.0 x 185.5 x 3.30 mm
