Apiquet/STI_Robotic_Competition_Mechanics/Prototype_Bottle_Mechanism/helical gear_3_gb.sldprt

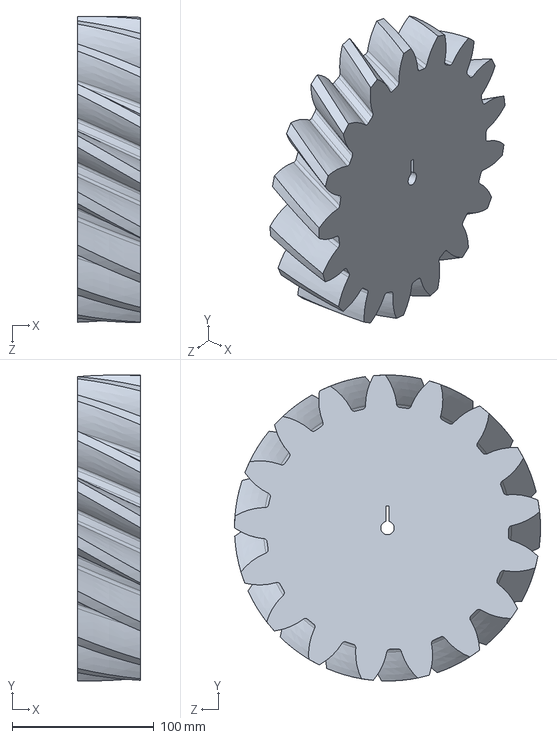
[picture p79: CAD file, 2019-03-18]
Prototype_Bottle_Mechanism/helical gear_3_gb.sldprt
44.5 x 216.3 x 216.3 mm
