Apiquet/STI_Robotic_Competition_Mechanics/Collector_Mechanism/Bottom_Motor_Holder.SLDPRT

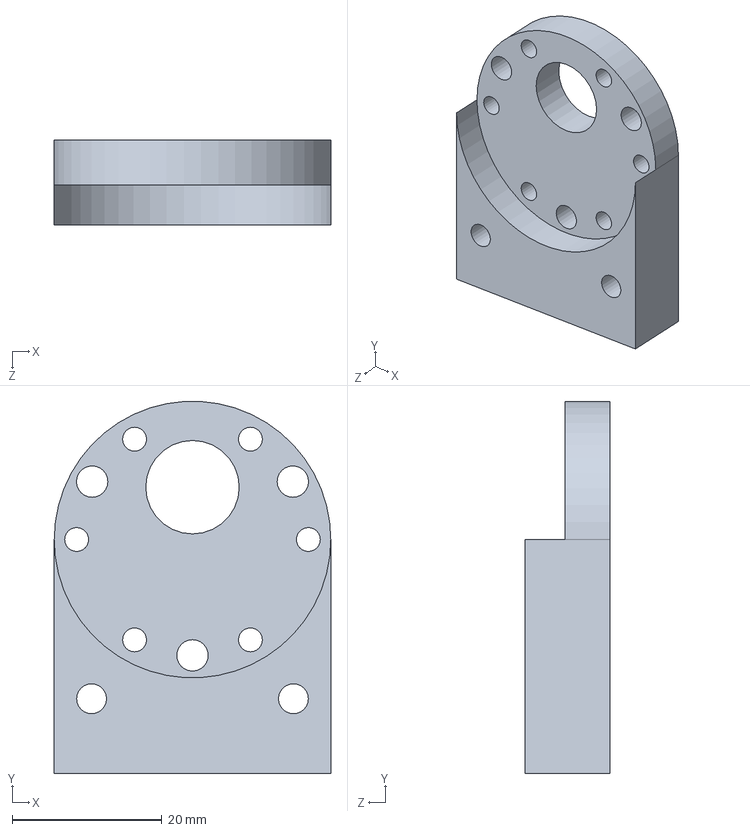
[picture p80: CAD file, 2019-04-24]
Collector_Mechanism/Bottom_Motor_Holder.SLDPRT
37.0 x 49.8 x 11.4 mm
