Apiquet/STI_Robotic_Competition_Mechanics/Divers/Panel_Bottom_Left_Side.SLDPRT

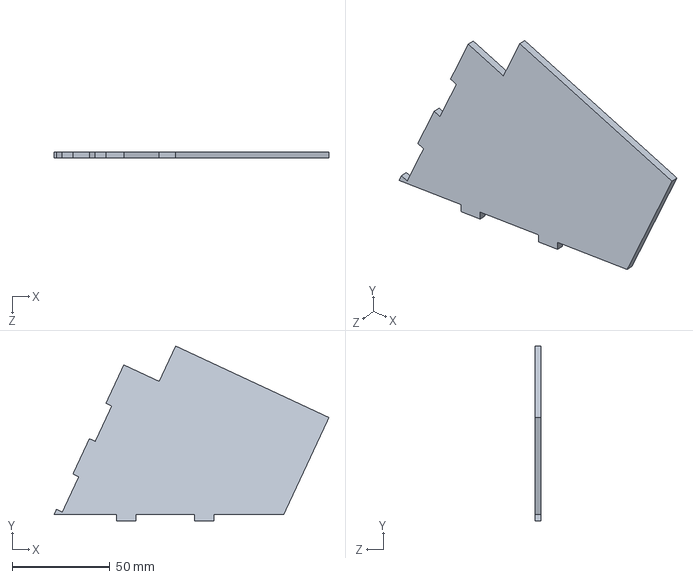
[picture p81: CAD file, 2019-05-30]
Divers/Panel_Bottom_Left_Side.SLDPRT
141.0 x 89.7 x 3.30 mm
