Apiquet/STI_Robotic_Competition_Mechanics/Drive_Base/Adapter_Wheel.sldprt

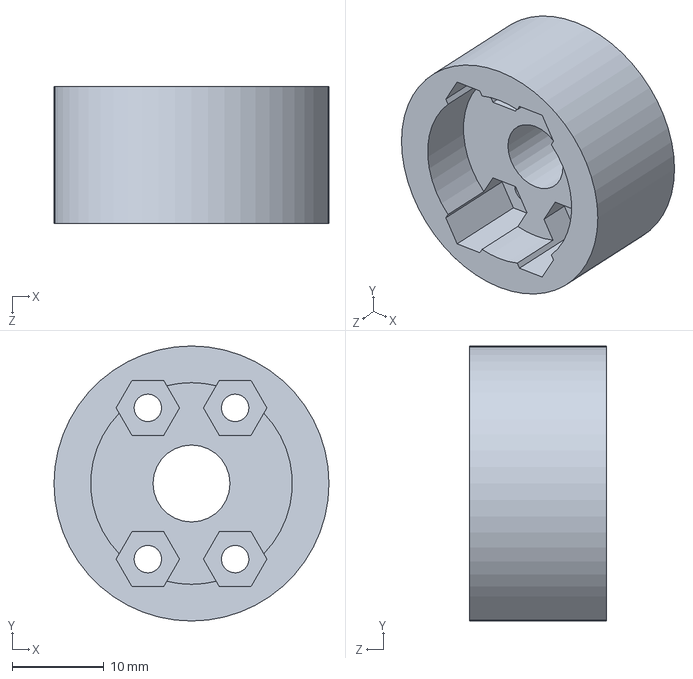
[picture p82: CAD file, 2019-04-24]
Drive_Base/Adapter_Wheel.sldprt
30.0 x 30.0 x 15.0 mm
