Apiquet/STI_Robotic_Competition_Mechanics/Prototype_Bottle_Mechanism/thin_roller_8mmAxis - Copy.SLDPRT

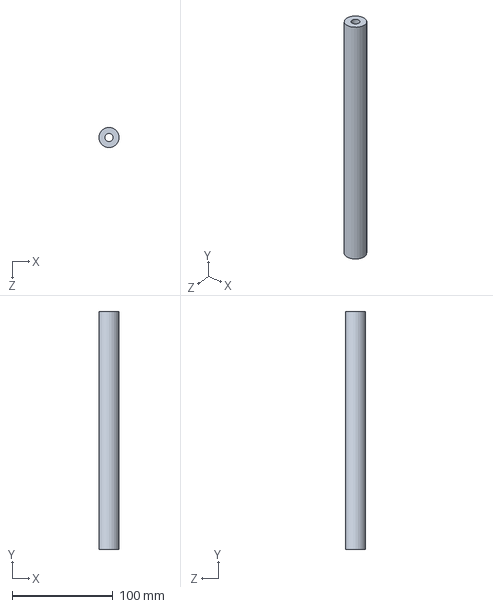
[picture p83: CAD file, 2019-03-18]
Prototype_Bottle_Mechanism/thin_roller_8mmAxis - Copy.SLDPRT
20.0 x 236.0 x 20.0 mm
