Apiquet/STI_Robotic_Competition_Mechanics/Collector_Mechanism/bevel_gear.sldprt

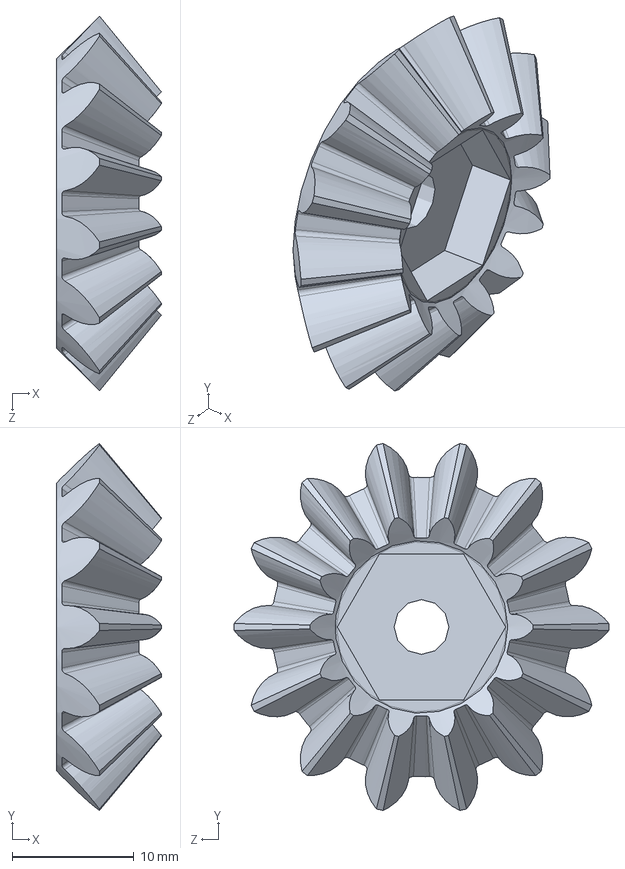
[picture p84: CAD file, 2019-04-24]
Collector_Mechanism/bevel_gear.sldprt
8.60 x 30.2 x 30.8 mm
