Apiquet/STI_Robotic_Competition_Mechanics/Divers/Panel_Bottom_Back.SLDPRT

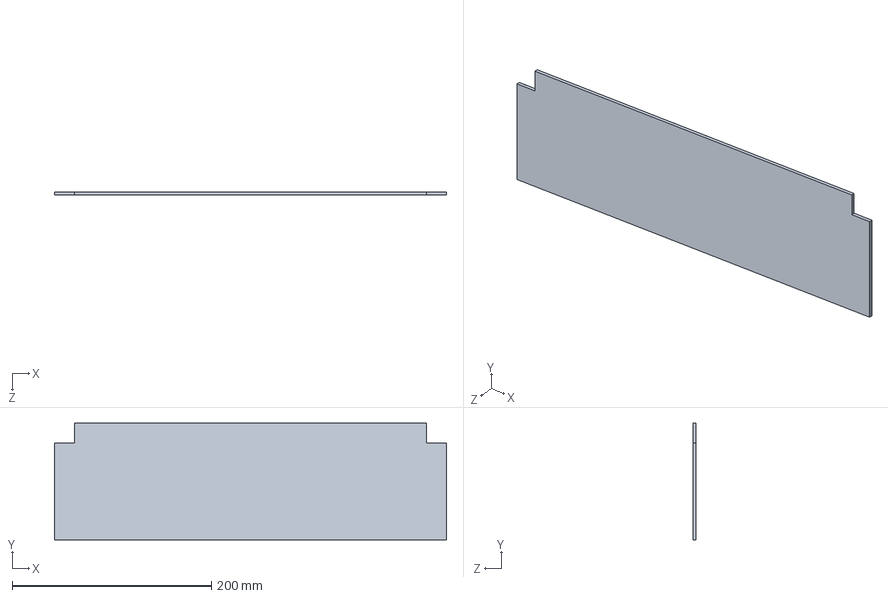
[picture p85: CAD file, 2019-05-30]
Divers/Panel_Bottom_Back.SLDPRT
393.4 x 117.0 x 3.30 mm
