Apiquet/STI_Robotic_Competition_Mechanics/Drive_Base/Wooden_Ramp_Support_Short.SLDPRT

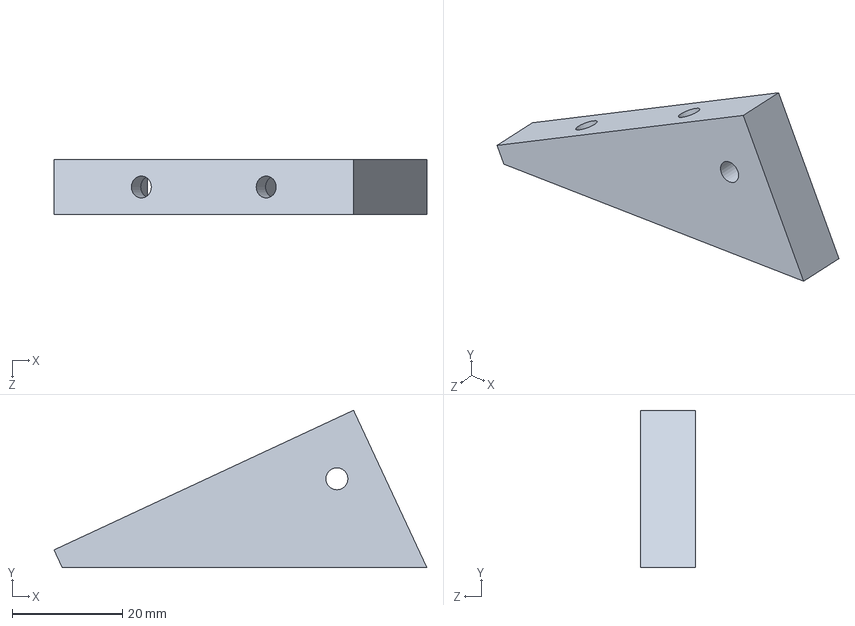
[picture p86: CAD file, 2019-04-24]
Drive_Base/Wooden_Ramp_Support_Short.SLDPRT
67.7 x 28.6 x 10.0 mm
