Apiquet/STI_Robotic_Competition_Mechanics/Prototype_Bottle_Mechanism/roller_holder_right_v2.SLDPRT

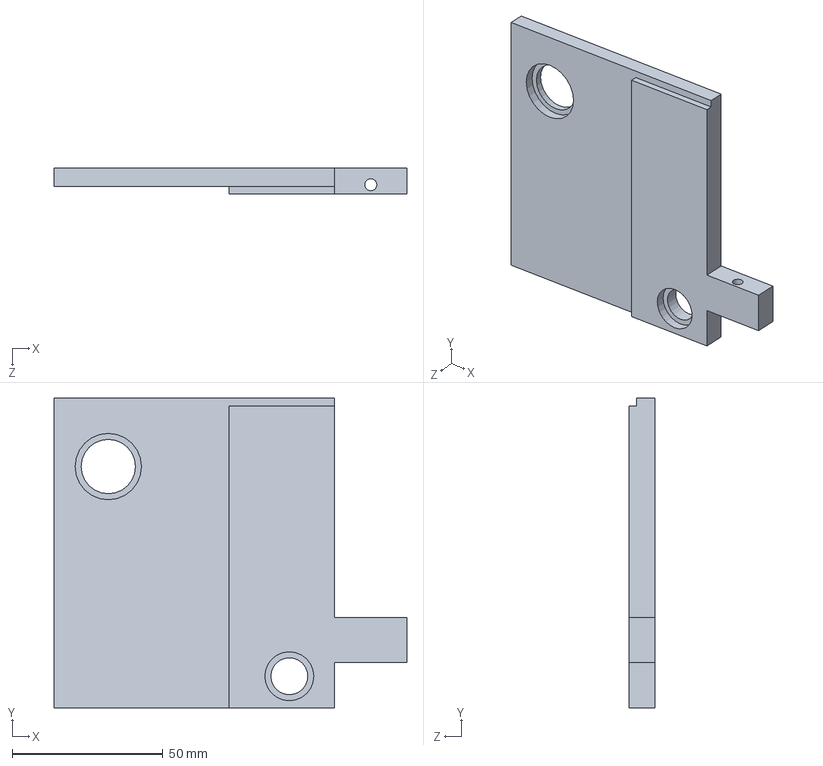
[picture p87: CAD file, 2019-03-17]
Prototype_Bottle_Mechanism/roller_holder_right_v2.SLDPRT
117.0 x 102.7 x 8.50 mm
