Apiquet/STI_Robotic_Competition_Mechanics/Divers/Panel_Top_Holder.SLDPRT

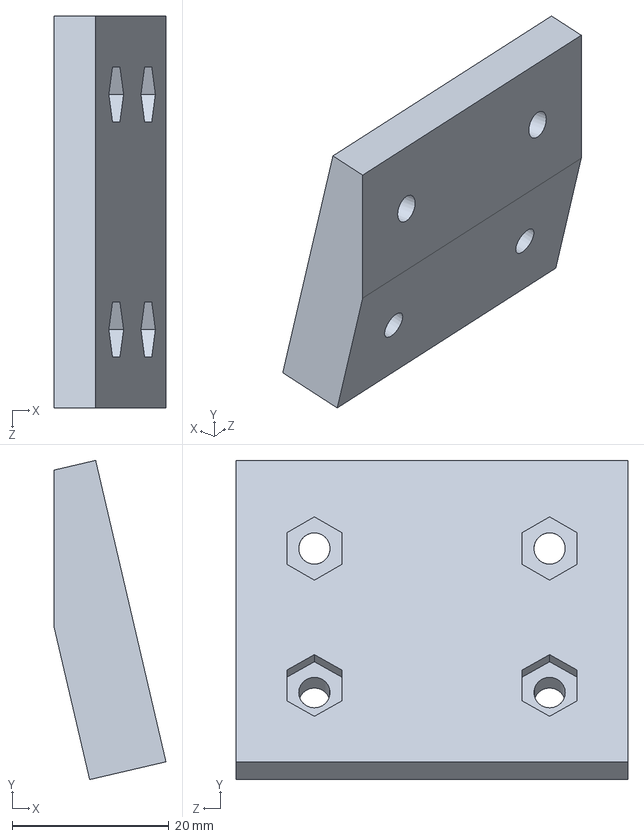
[picture p88: CAD file, 2019-05-30]
Divers/Panel_Top_Holder.SLDPRT
14.3 x 40.7 x 50.0 mm
