Apiquet/STI_Robotic_Competition_Mechanics/Divers/Panel_Bottom_Front.SLDPRT

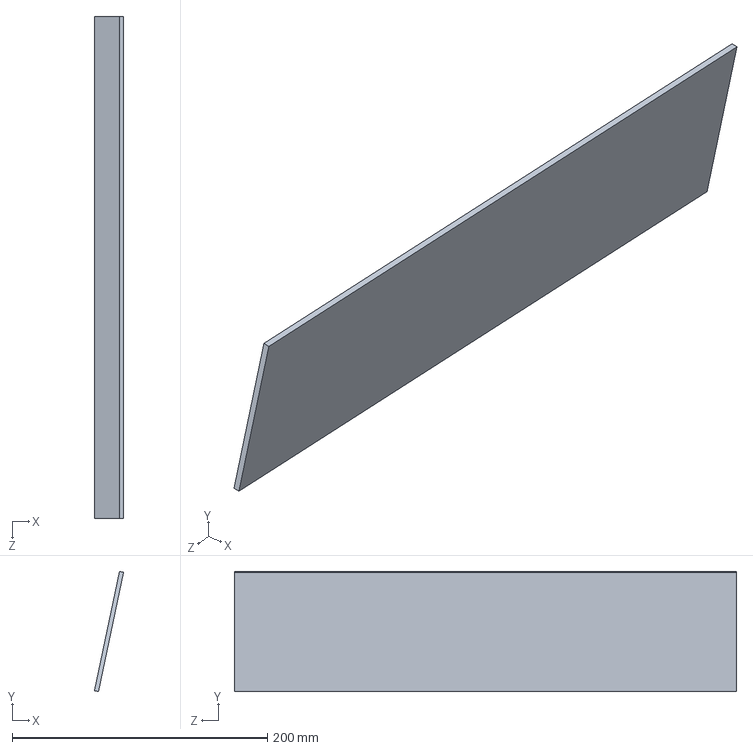
[picture p89: CAD file, 2019-05-20]
Divers/Panel_Bottom_Front.SLDPRT
22.9 x 94.1 x 393.4 mm
