Apiquet/STI_Robotic_Competition_Mechanics/Drive_Base/Body_Base.SLDPRT

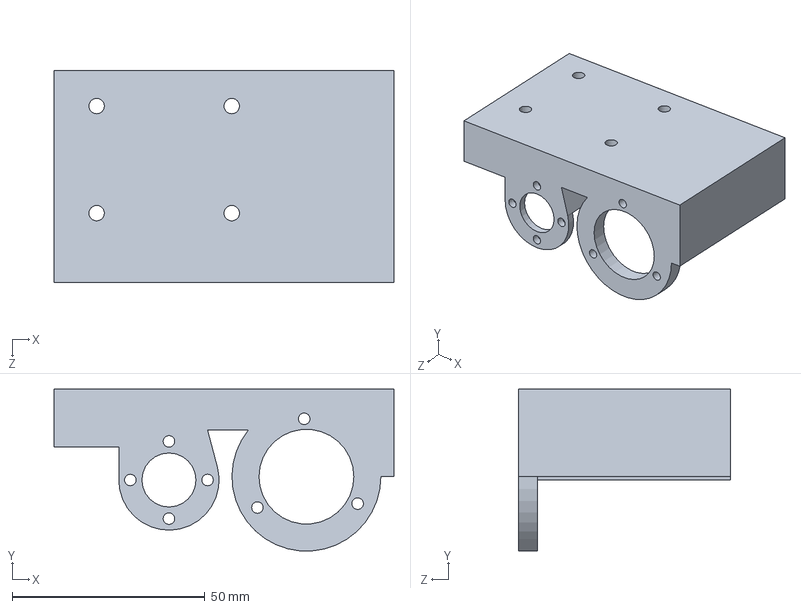
[picture p90: CAD file, 2019-04-21]
Drive_Base/Body_Base.SLDPRT
88.1 x 41.9 x 55.0 mm
