Apiquet/STI_Robotic_Competition_Mechanics/Prototype_Bottle_Mechanism/roller_holder_template.SLDPRT

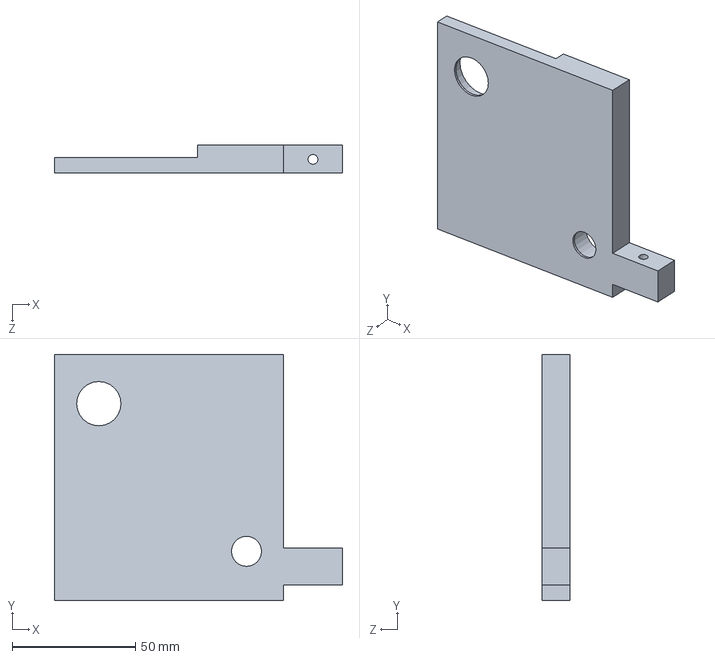
[picture p91: CAD file, 2019-03-16]
Prototype_Bottle_Mechanism/roller_holder_template.SLDPRT
117.0 x 100.0 x 11.3 mm
