Apiquet/STI_Robotic_Competition_Mechanics/Collector_Mechanism/10-tooth sprocket.SLDPRT

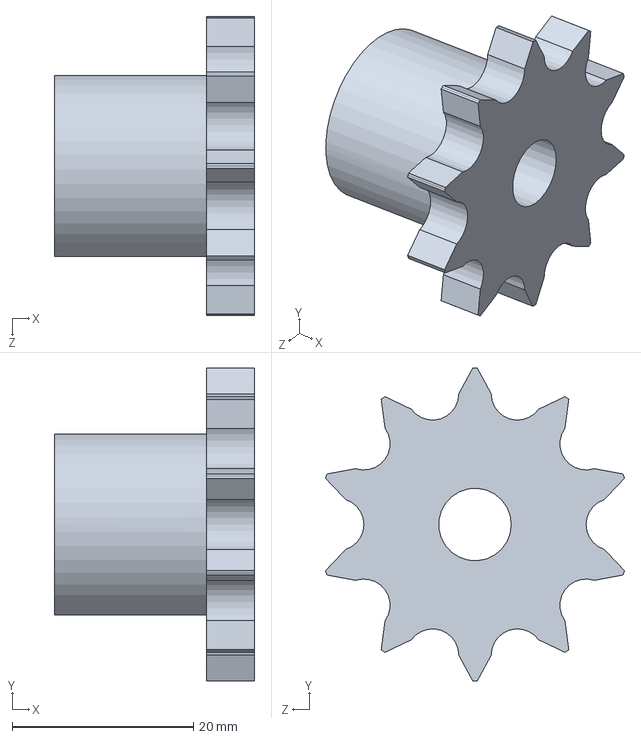
[picture p92: CAD file, 2019-04-24]
Collector_Mechanism/10-tooth sprocket.SLDPRT
22.1 x 34.5 x 33.0 mm
