Apiquet/STI_Robotic_Competition_Mechanics/Divers/Panel_Top_Front.SLDPRT

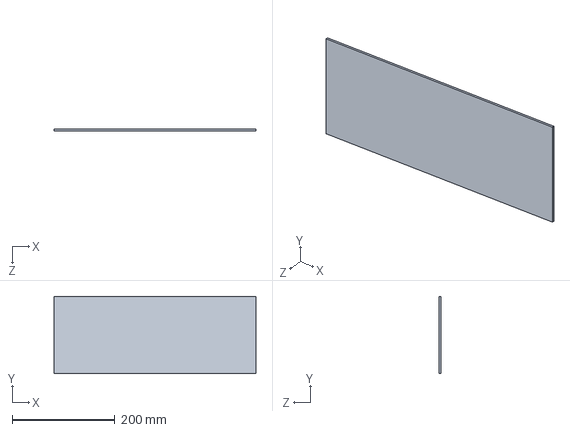
[picture p93: CAD file, 2019-05-14]
Divers/Panel_Top_Front.SLDPRT
393.4 x 150.0 x 3.30 mm
