Apiquet/STI_Robotic_Competition_Mechanics/Drive_Base/Bearing Holder.SLDPRT

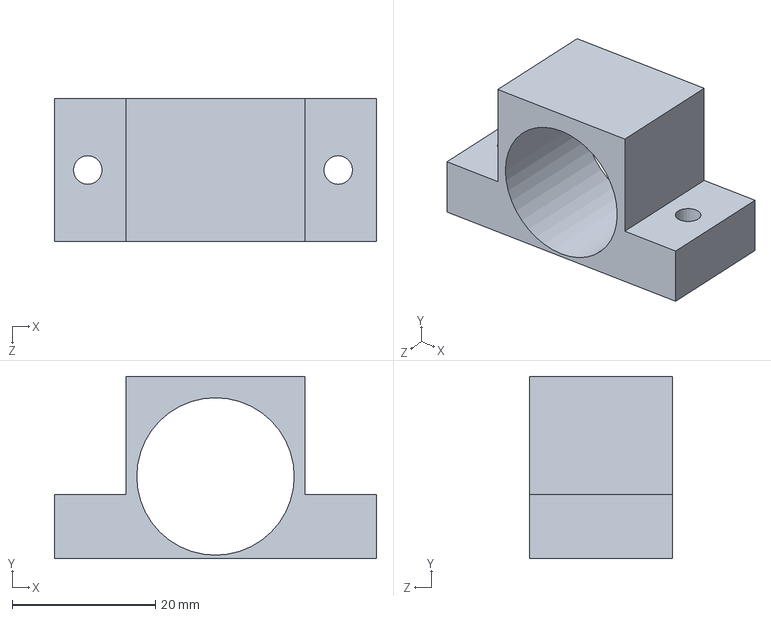
[picture p94: CAD file, 2019-04-21]
Drive_Base/Bearing Holder.SLDPRT
45.0 x 25.5 x 20.0 mm
