Apiquet/STI_Robotic_Competition_Mechanics/Prototype_Bottle_Mechanism/10mmAxis.SLDPRT

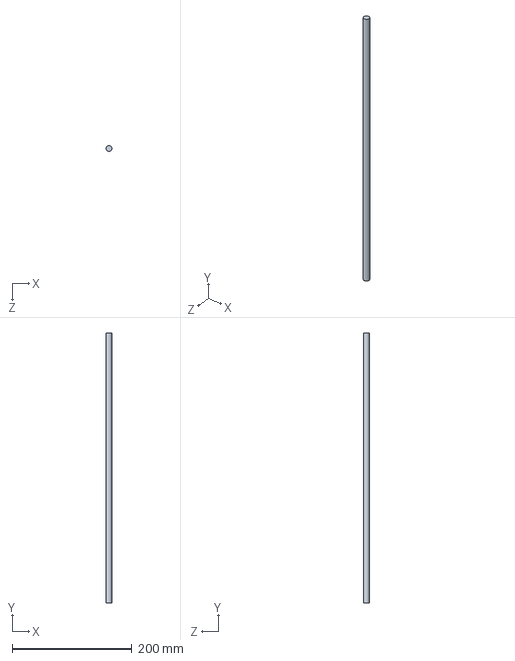
[picture p95: CAD file, 2019-03-16]
Prototype_Bottle_Mechanism/10mmAxis.SLDPRT
10.0 x 450.0 x 10.0 mm
