Apiquet/STI_Robotic_Competition_Mechanics/Collector_Mechanism/Gear_Sprocket_Adapter.SLDPRT

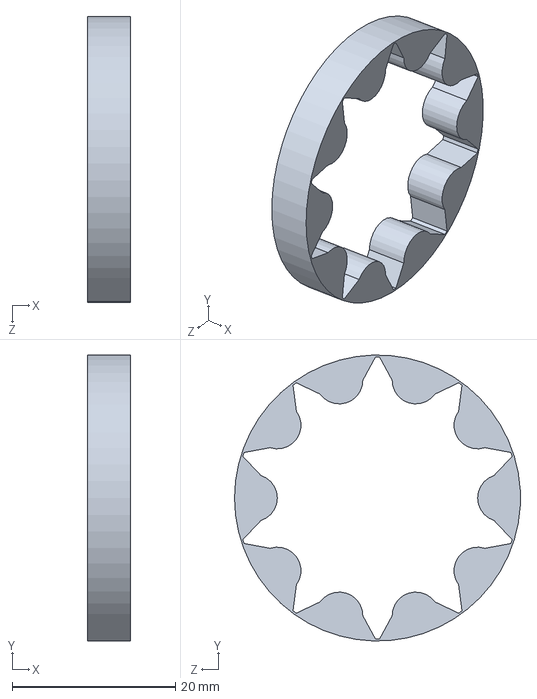
[picture p96: CAD file, 2019-04-24]
Collector_Mechanism/Gear_Sprocket_Adapter.SLDPRT
5.30 x 35.0 x 35.0 mm
