Apiquet/STI_Robotic_Competition_Mechanics/Divers/Battery_Side_Block.SLDPRT

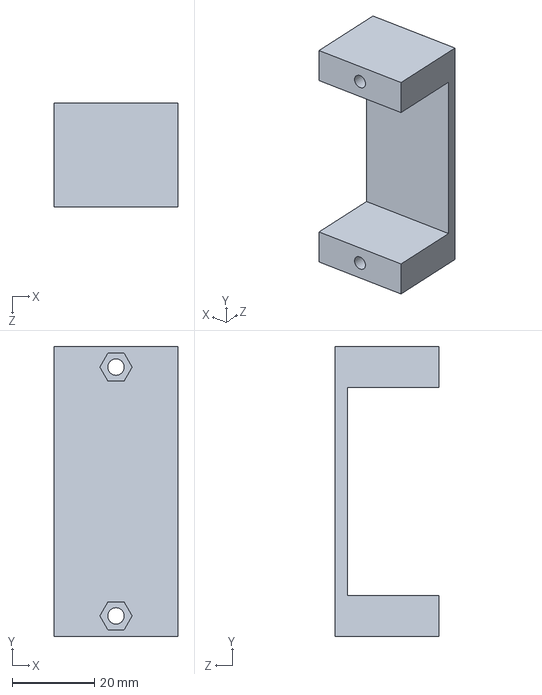
[picture p97: CAD file, 2019-05-12]
Divers/Battery_Side_Block.SLDPRT
30.0 x 70.4 x 25.3 mm
