Apiquet/STI_Robotic_Competition_Mechanics/Prototype_Bottle_Mechanism/planke.SLDPRT

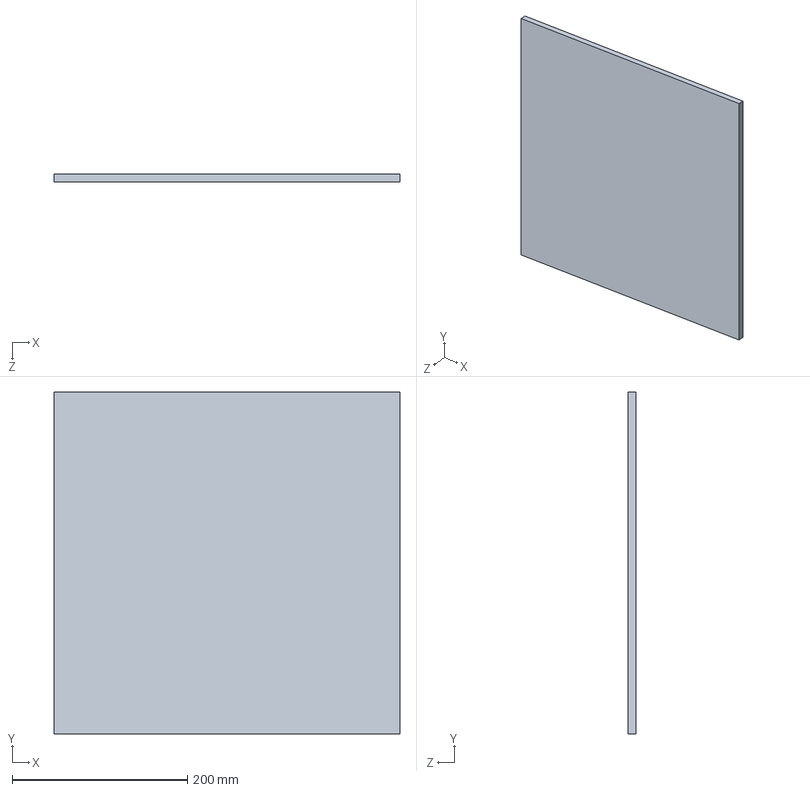
[picture p98: CAD file, 2019-03-16]
Prototype_Bottle_Mechanism/planke.SLDPRT
395.0 x 390.0 x 9.00 mm
