Apiquet/STI_Robotic_Competition_Mechanics/Divers/Axis_Lock.SLDPRT

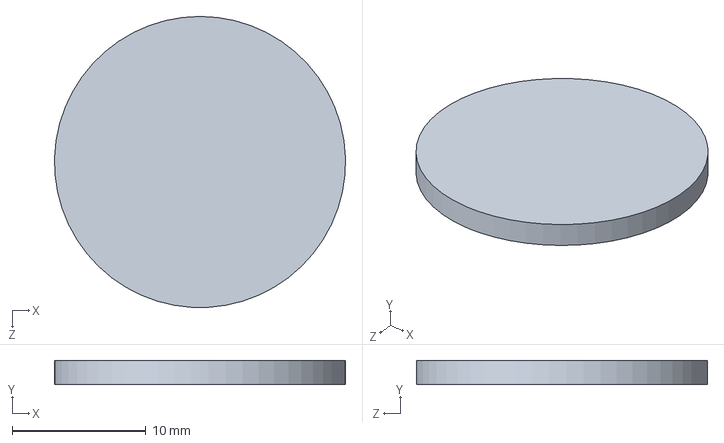
[picture p99: CAD file, 2019-05-09]
Divers/Axis_Lock.SLDPRT
21.8 x 1.80 x 21.8 mm
