Apiquet/STI_Robotic_Competition_Mechanics/Drive_Base/Bearing Holder Long.SLDPRT

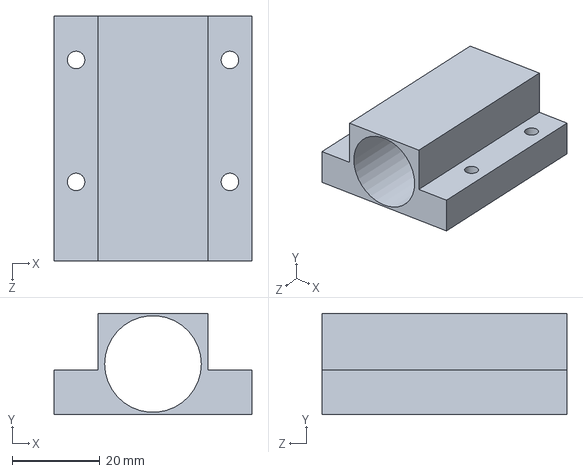
[picture p100: CAD file, 2019-04-21]
Drive_Base/Bearing Holder Long.SLDPRT
45.0 x 23.0 x 55.8 mm
