Apiquet/STI_Robotic_Competition_Mechanics/Collector_Mechanism/hex_hub.SLDPRT

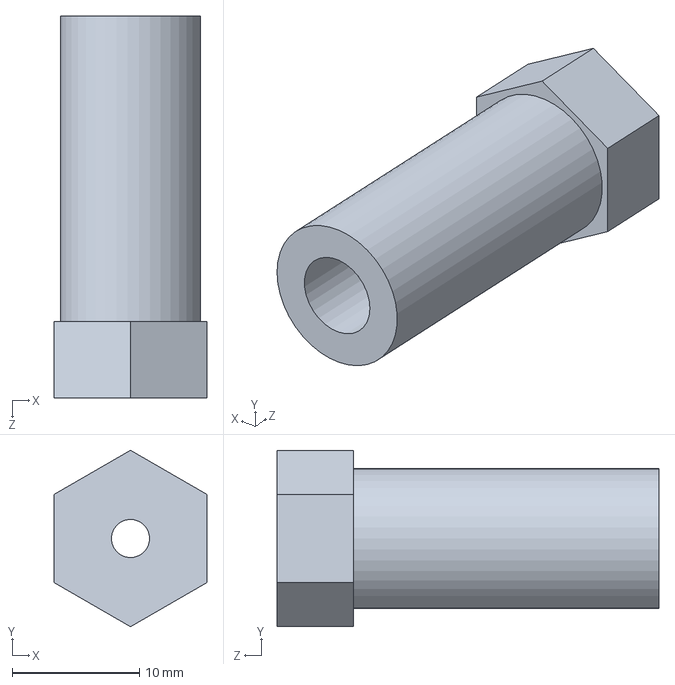
[picture p101: CAD file, 2019-04-21]
Collector_Mechanism/hex_hub.SLDPRT
12.0 x 13.9 x 30.0 mm
