Apiquet/STI_Robotic_Competition_Mechanics/Divers/Wood_base.STEP

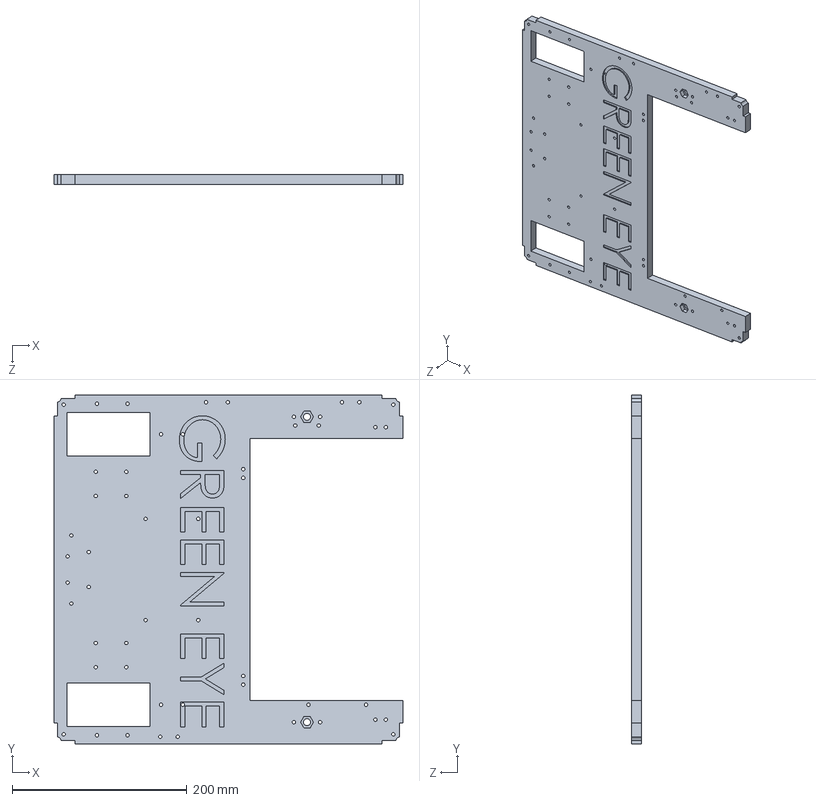
[picture p102: CAD file, 2019-05-06]
Divers/Wood_base.STEP
400.0 x 400.0 x 11.7 mm
