Apiquet/STI_Robotic_Competition_Mechanics/Drive_Base/Ball_support.SLDPRT

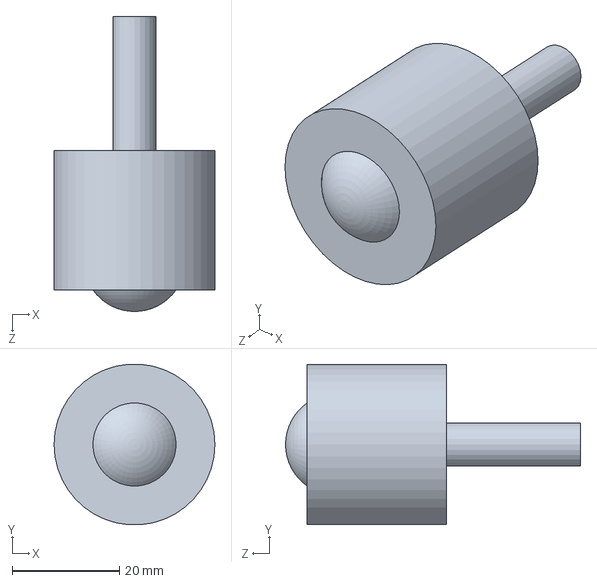
[picture p103: CAD file, 2019-04-21]
Drive_Base/Ball_support.SLDPRT
30.0 x 29.9 x 55.0 mm
