Apiquet/STI_Robotic_Competition_Mechanics/Prototype_Bottle_Mechanism/8mmAxis_then_6mm.SLDPRT

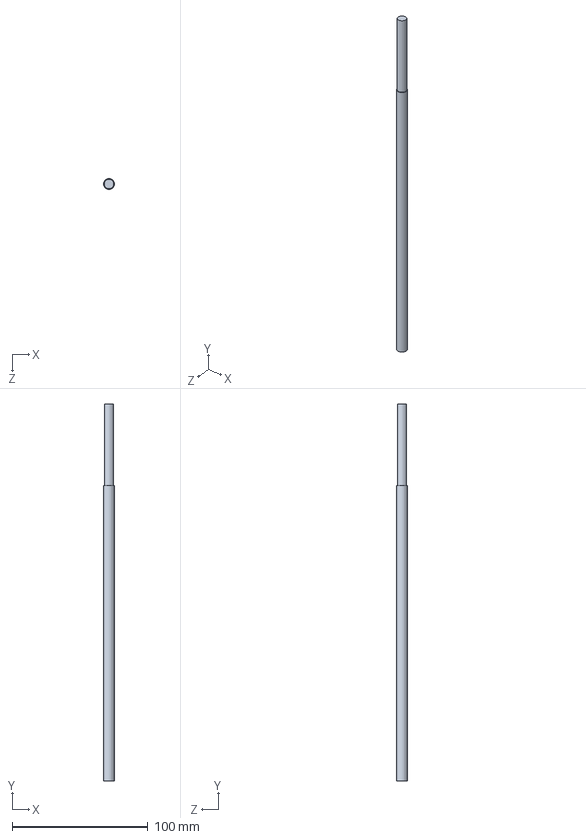
[picture p104: CAD file, 2019-03-16]
Prototype_Bottle_Mechanism/8mmAxis_then_6mm.SLDPRT
8.00 x 278.0 x 8.00 mm
