Apiquet/STI_Robotic_Competition_Mechanics/Collector_Mechanism/Gear_Sprocket.SLDPRT

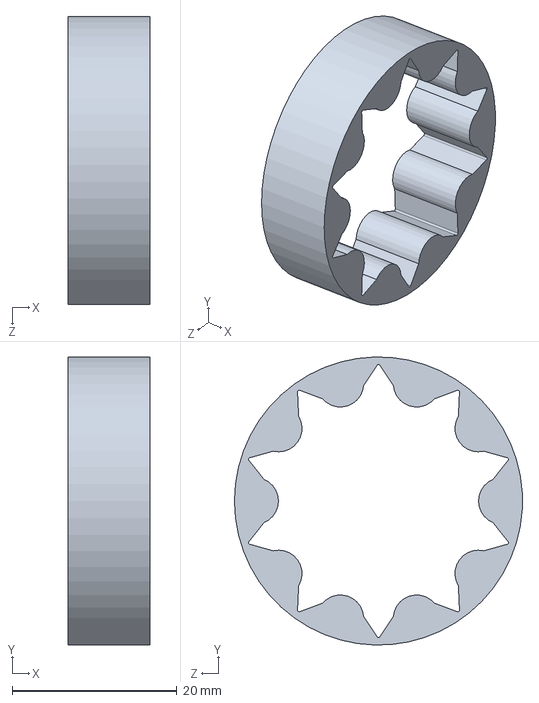
[picture p105: CAD file, 2019-04-21]
Collector_Mechanism/Gear_Sprocket.SLDPRT
10.0 x 35.0 x 35.0 mm
