Apiquet/STI_Robotic_Competition_Mechanics/Collector_Mechanism/Roller_Top.SLDPRT

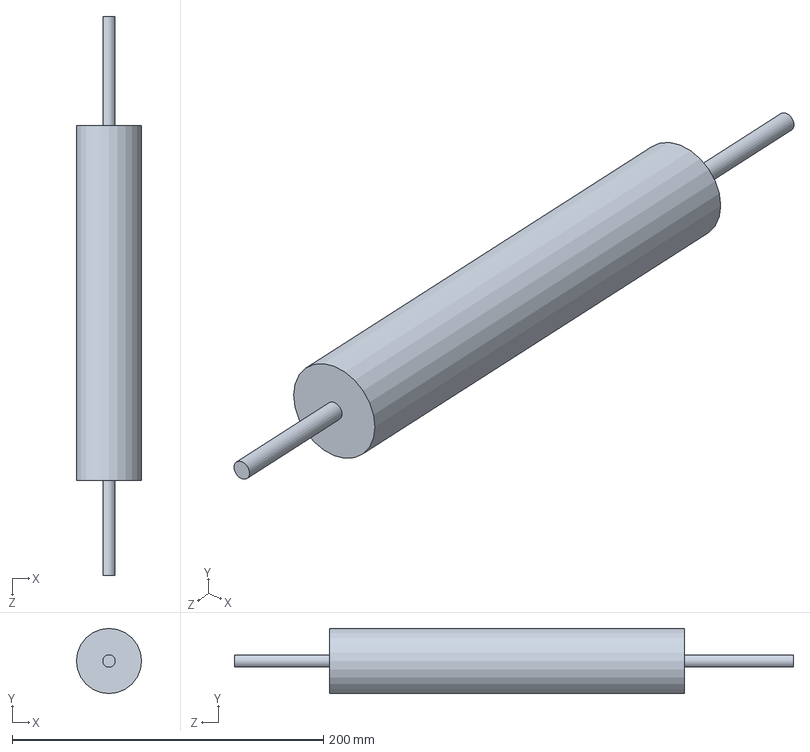
[picture p107: CAD file, 2019-04-21]
Collector_Mechanism/Roller_Top.SLDPRT
41.9 x 41.9 x 359.0 mm
