Apiquet/STI_Robotic_Competition_Mechanics/Divers/Panel_Top_Front_Square.SLDPRT

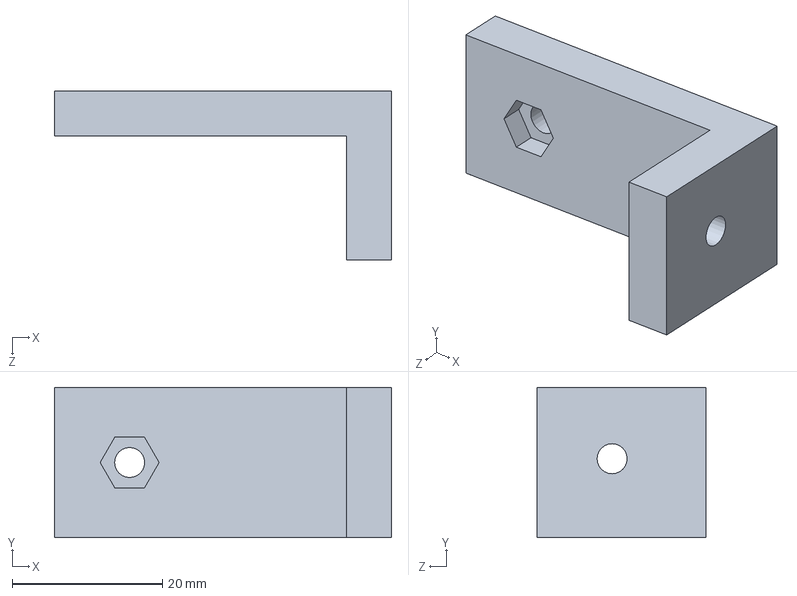
[picture p108: CAD file, 2019-05-05]
Divers/Panel_Top_Front_Square.SLDPRT
44.8 x 20.0 x 22.5 mm
