Apiquet/STI_Robotic_Competition_Mechanics/Drive_Base/wheel.SLDPRT

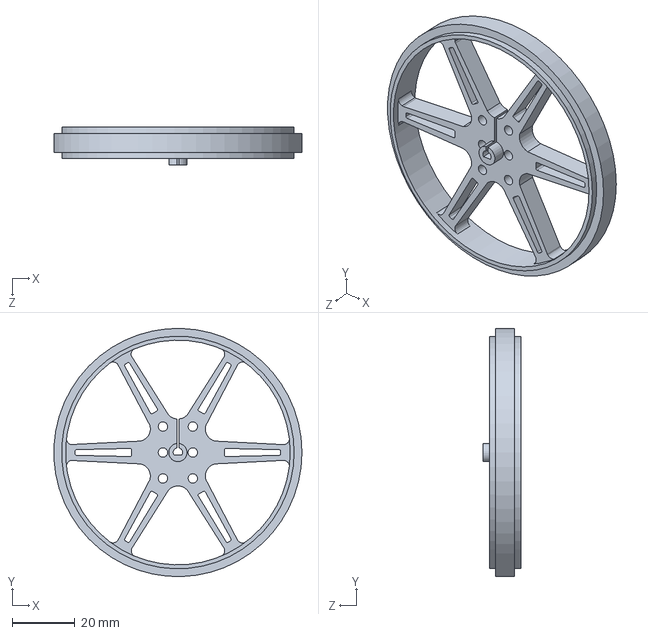
[picture p109: CAD file, 2019-04-19]
Drive_Base/wheel.SLDPRT
78.9 x 79.0 x 12.0 mm
