Apiquet/STI_Robotic_Competition_Mechanics/Collector_Mechanism/Bearing16_7.9_5mm.SLDPRT

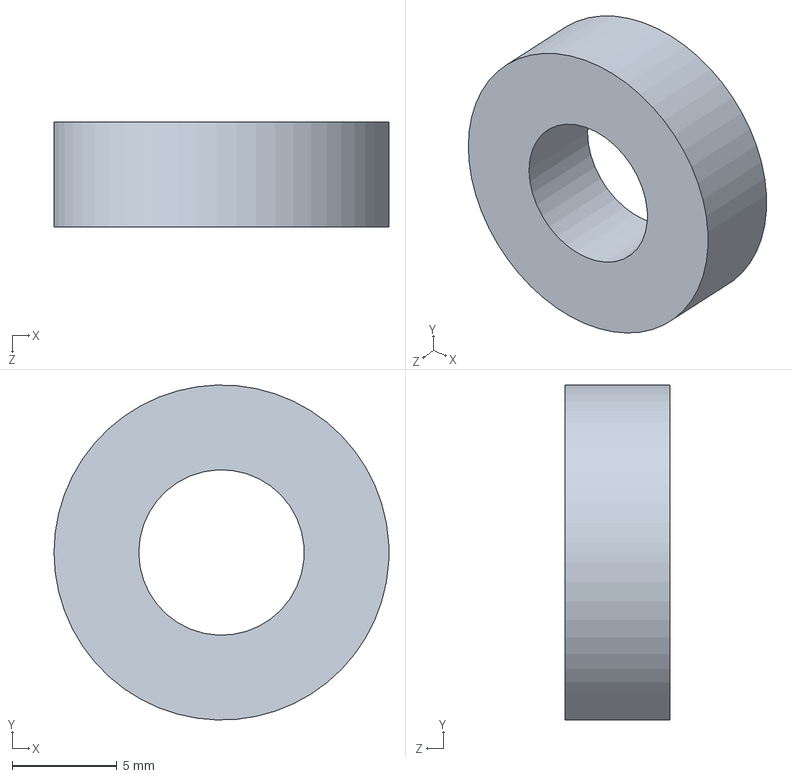
[picture p110: CAD file, 2019-03-20]
Collector_Mechanism/Bearing16_7.9_5mm.SLDPRT
16.0 x 16.0 x 5.00 mm
