Apiquet/STI_Robotic_Competition_Mechanics/Divers/Corner_Roof.SLDPRT

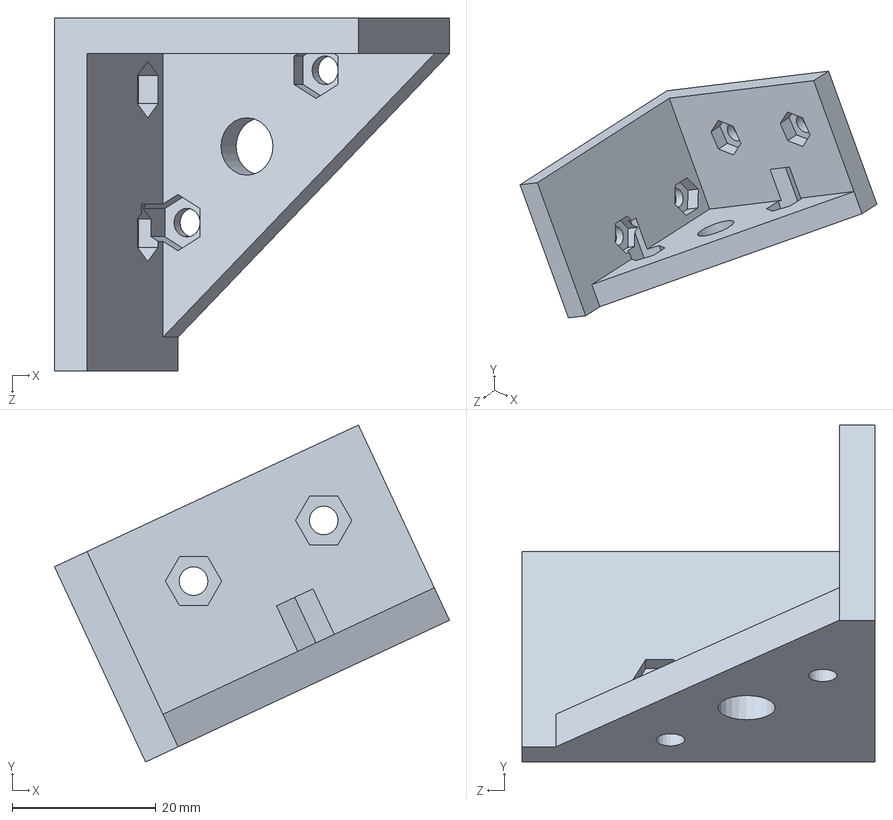
[picture p111: CAD file, 2019-05-05]
Divers/Corner_Roof.SLDPRT
55.0 x 46.9 x 49.2 mm
