Apiquet/STI_Robotic_Competition_Mechanics/Collector_Mechanism/Bearing15_5.9_5mm.SLDPRT

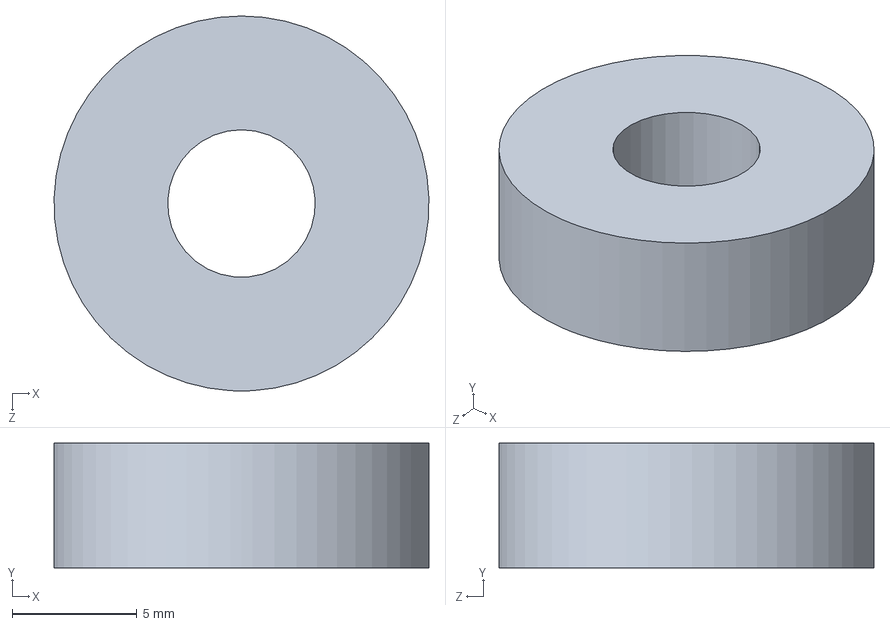
[picture p112: CAD file, 2019-03-20]
Collector_Mechanism/Bearing15_5.9_5mm.SLDPRT
15.0 x 5.00 x 15.0 mm
