Apiquet/STI_Robotic_Competition_Mechanics/Prototype_Bottle_Mechanism/Small_gear_Roller1.SLDPRT

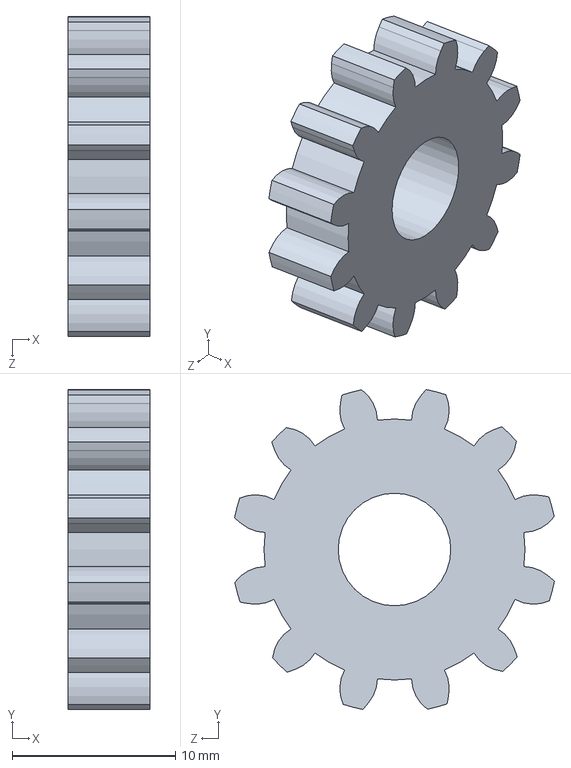
[picture p113: CAD file, 2019-03-13]
Prototype_Bottle_Mechanism/Small_gear_Roller1.SLDPRT
5.00 x 19.6 x 19.6 mm
