Apiquet/STI_Robotic_Competition_Mechanics/Collector_Mechanism/Ball Bearing 608ZZ.SLDPRT

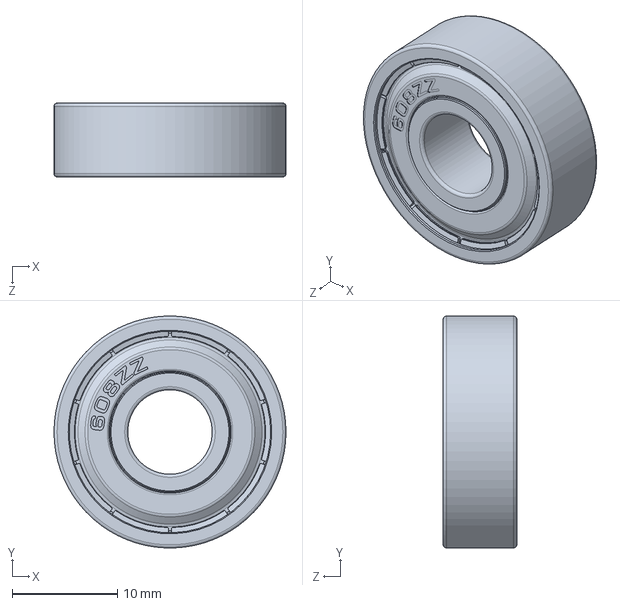
[picture p114: CAD file, 2019-03-20]
Collector_Mechanism/Ball Bearing 608ZZ.SLDPRT
22.0 x 22.0 x 7.00 mm
