Apiquet/STI_Robotic_Competition_Mechanics/Divers/Battery_Blocker.SLDPRT

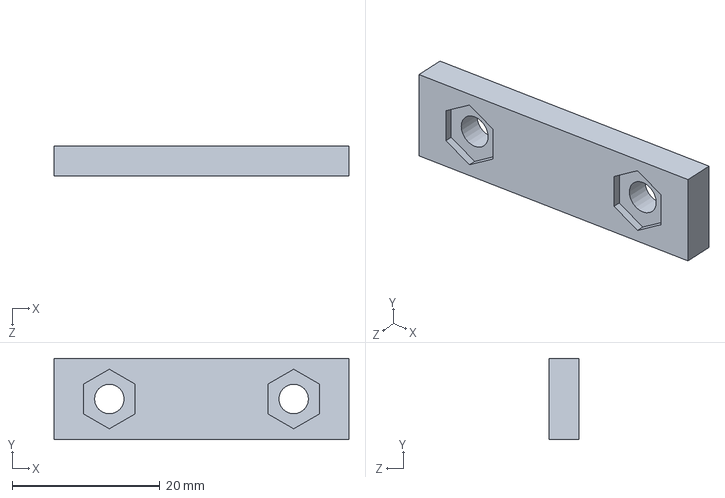
[picture p115: CAD file, 2019-05-05]
Divers/Battery_Blocker.SLDPRT
40.0 x 11.0 x 4.00 mm
