Apiquet/STI_Robotic_Competition_Mechanics/Drive_Base/Base_support_wheel.SLDPRT

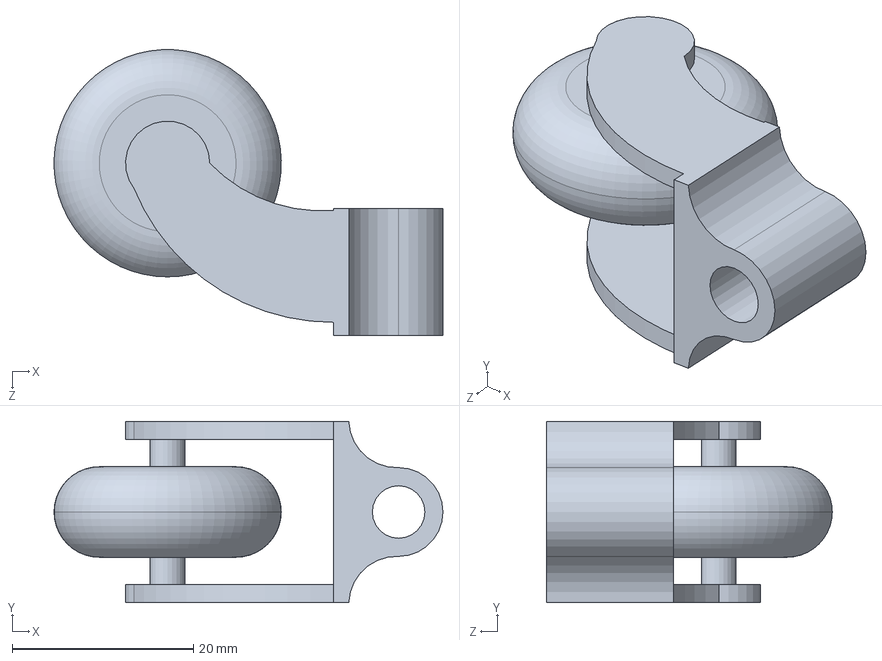
[picture p116: CAD file, 2019-04-19]
Drive_Base/Base_support_wheel.SLDPRT
42.9 x 20.0 x 31.5 mm
