Apiquet/STI_Robotic_Competition_Mechanics/Divers/Panel_Roof3.DXF

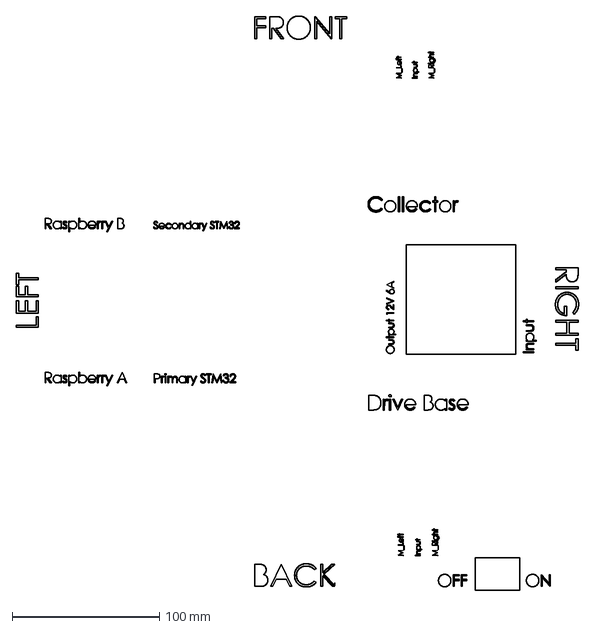
[picture p117: CAD file, 2019-04-24]
Divers/Panel_Roof3.DXF
381.4 x 389.3 mm
