Apiquet/STI_Robotic_Competition_Mechanics/Drive_Base/WheelBall_Simulation.SLDPRT

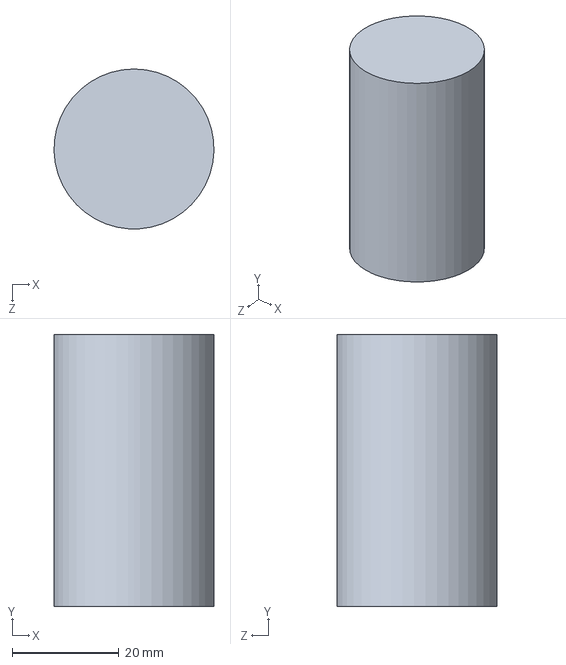
[picture p118: CAD file, 2019-04-19]
Drive_Base/WheelBall_Simulation.SLDPRT
30.0 x 51.0 x 30.0 mm
