Apiquet/STI_Robotic_Competition_Mechanics/Prototype_Bottle_Mechanism/LED STRIP FOOT.SLDPRT

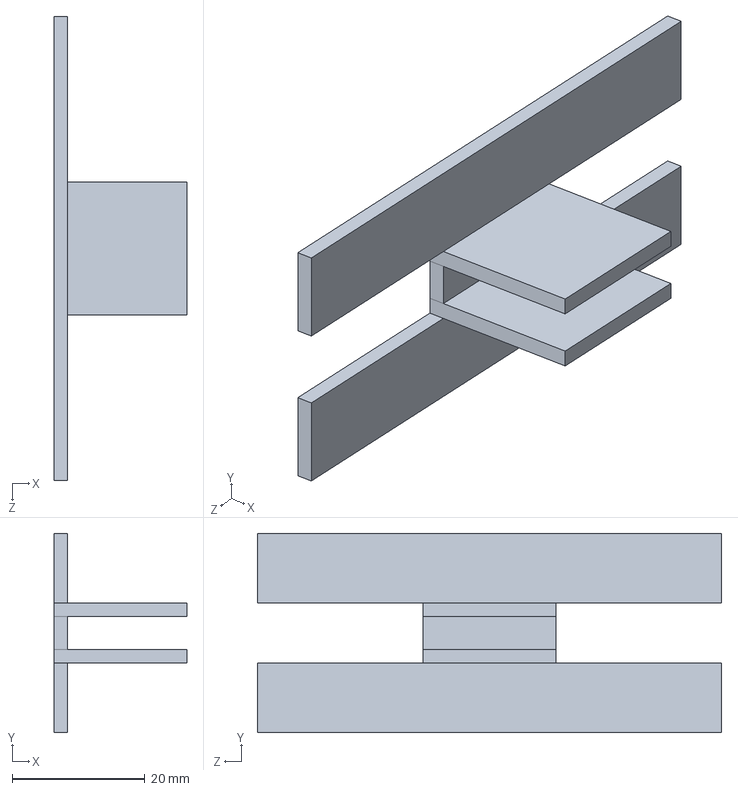
[picture p119: CAD file, 2019-03-12]
Prototype_Bottle_Mechanism/LED STRIP FOOT.SLDPRT
20.0 x 30.0 x 70.0 mm
