Apiquet/STI_Robotic_Competition_Mechanics/Divers/Panel_Roof2.DXF

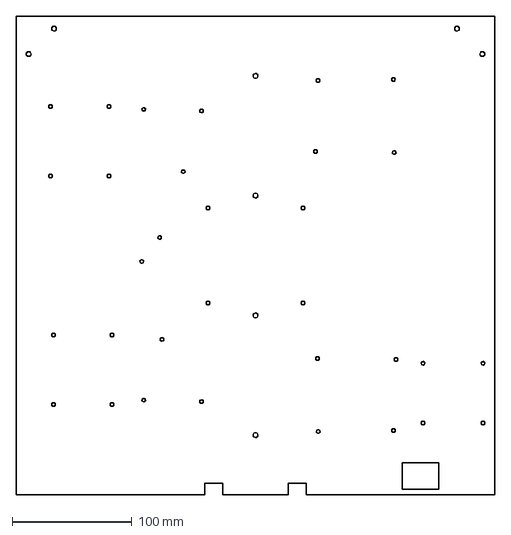
[picture p120: CAD file, 2019-04-24]
Divers/Panel_Roof2.DXF
400.0 x 400.0 mm
