Apiquet/STI_Robotic_Competition_Mechanics/Drive_Base/MirrorSpacer_front_wheel.SLDPRT

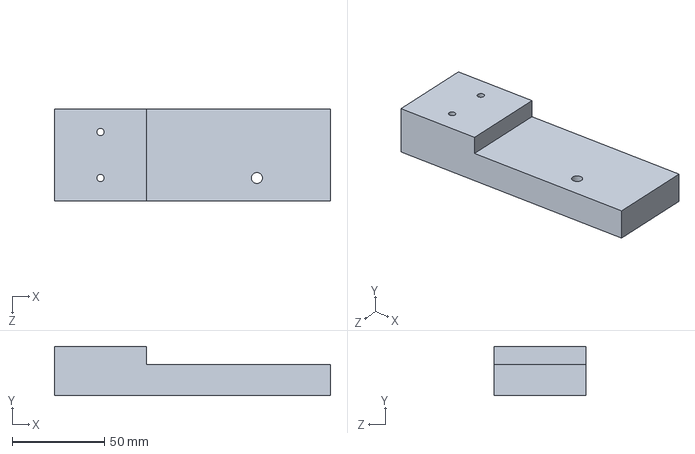
[picture p121: CAD file, 2019-04-19]
Drive_Base/MirrorSpacer_front_wheel.SLDPRT
150.0 x 26.8 x 50.0 mm
