Apiquet/STI_Robotic_Competition_Mechanics/Prototype_Bottle_Mechanism/Bearing_Holder.SLDPRT

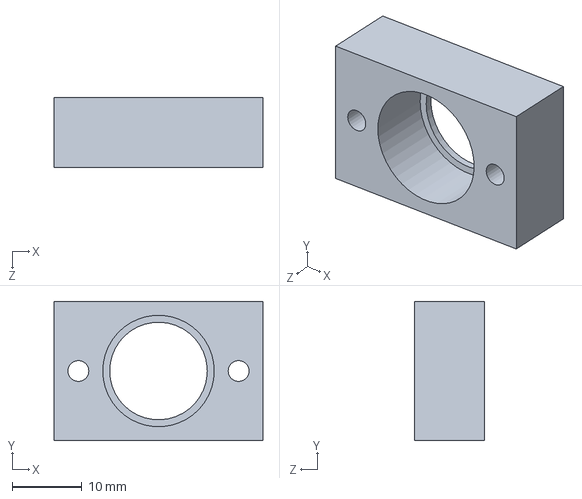
[picture p122: CAD file, 2019-03-12]
Prototype_Bottle_Mechanism/Bearing_Holder.SLDPRT
30.0 x 20.0 x 10.0 mm
