Apiquet/STI_Robotic_Competition_Mechanics/Divers/NUCLEO-F411RE.SLDPRT

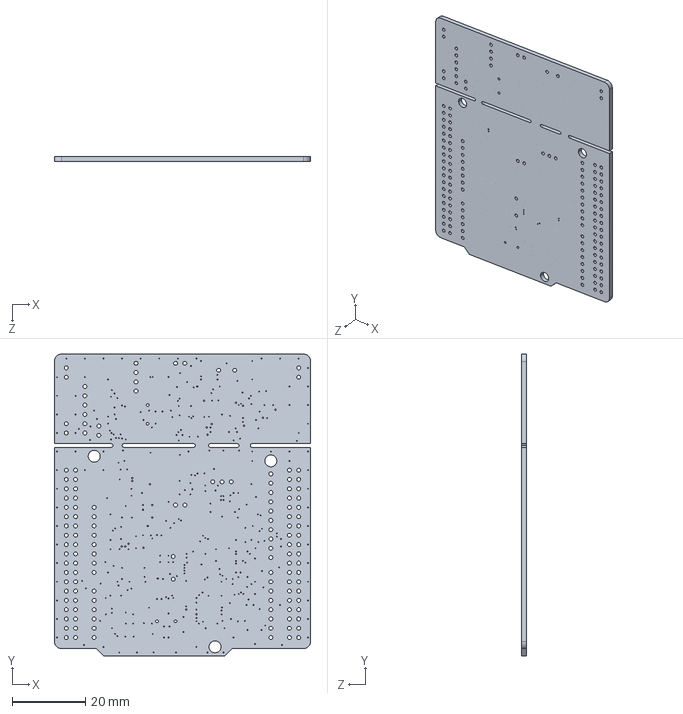
[picture p123: CAD file, 2019-04-24]
Divers/NUCLEO-F411RE.SLDPRT
70.0 x 82.5 x 1.50 mm
