Apiquet/STI_Robotic_Competition_Mechanics/Prototype_Bottle_Mechanism/Foam.SLDPRT

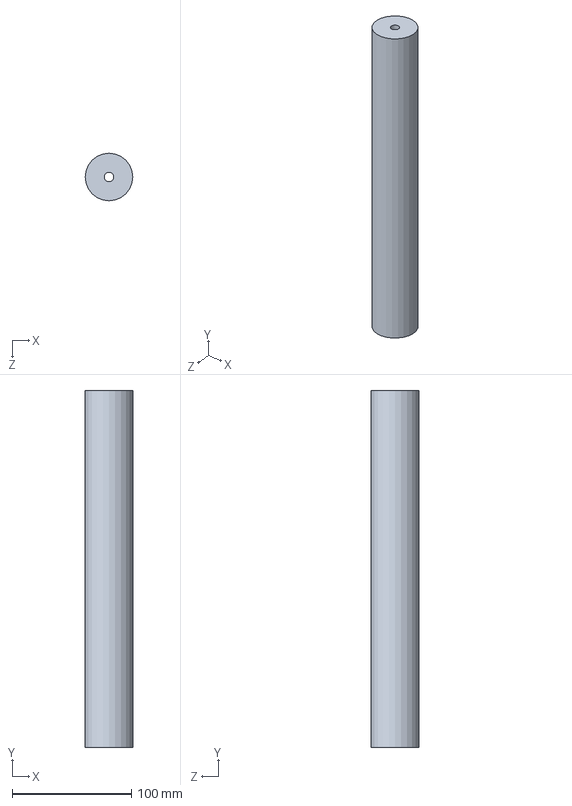
[picture p124: CAD file, 2019-03-12]
Prototype_Bottle_Mechanism/Foam.SLDPRT
40.0 x 300.0 x 40.0 mm
