Apiquet/STI_Robotic_Competition_Mechanics/Divers/Panel_Right_Holder.SLDPRT

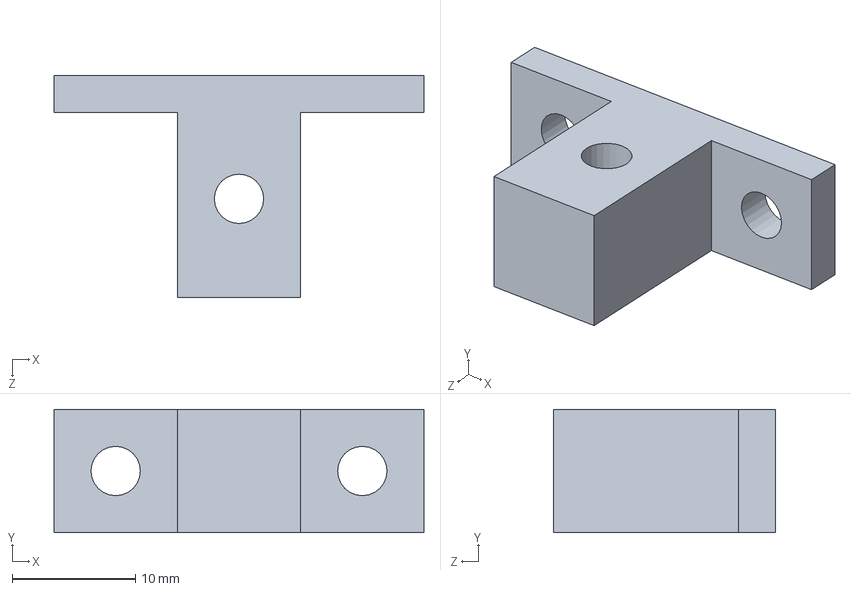
[picture p125: CAD file, 2019-04-24]
Divers/Panel_Right_Holder.SLDPRT
30.0 x 10.0 x 18.0 mm
