Apiquet/STI_Robotic_Competition_Mechanics/Drive_Base/Spacer_front_wheel.SLDPRT

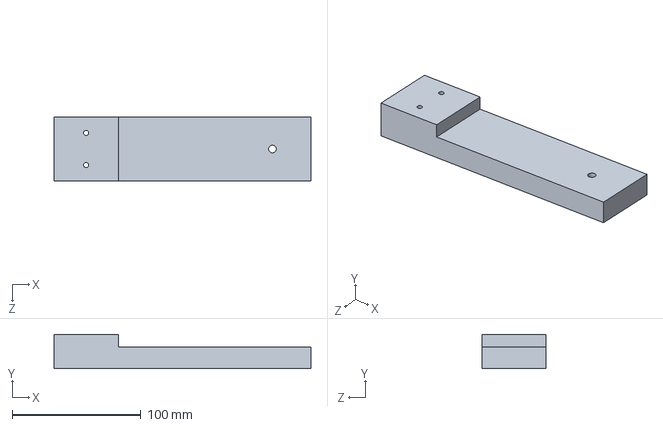
[picture p126: CAD file, 2019-03-27]
Drive_Base/Spacer_front_wheel.SLDPRT
200.0 x 26.8 x 50.0 mm
