Apiquet/STI_Robotic_Competition_Mechanics/Prototype_Bottle_Mechanism/Holder_2_roller.sldprt

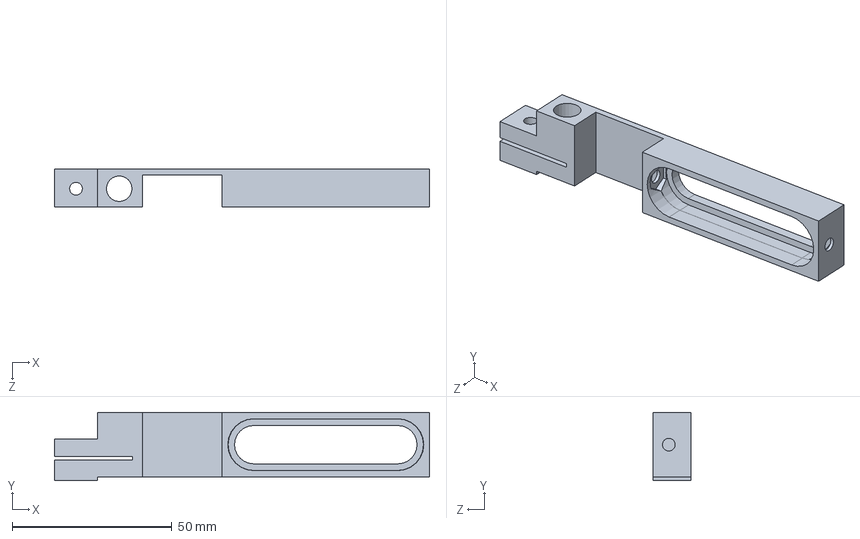
[picture p127: CAD file, 2019-03-12]
Prototype_Bottle_Mechanism/Holder_2_roller.sldprt
117.5 x 21.4 x 12.0 mm
