Apiquet/STI_Robotic_Competition_Mechanics/Divers/Rpi3Bplus.SLDPRT

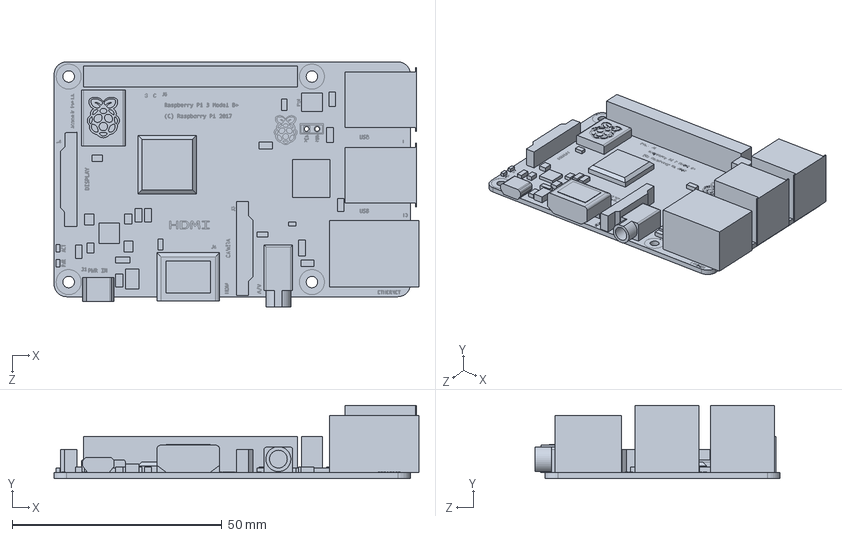
[picture p128: CAD file, 2019-04-24]
Divers/Rpi3Bplus.SLDPRT
87.0 x 17.5 x 58.5 mm
