Apiquet/STI_Robotic_Competition_Mechanics/Drive_Base/Gear_Moteur.SLDPRT

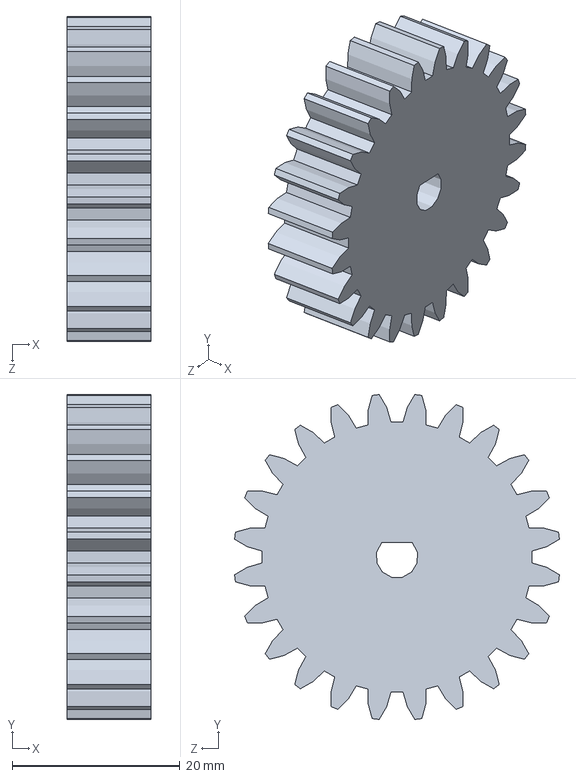
[picture p129: CAD file, 2019-03-24]
Drive_Base/Gear_Moteur.SLDPRT
10.0 x 38.8 x 38.8 mm
