Apiquet/STI_Robotic_Competition_Mechanics/Prototype_Bottle_Mechanism/Holder_1_roller_long.SLDPRT

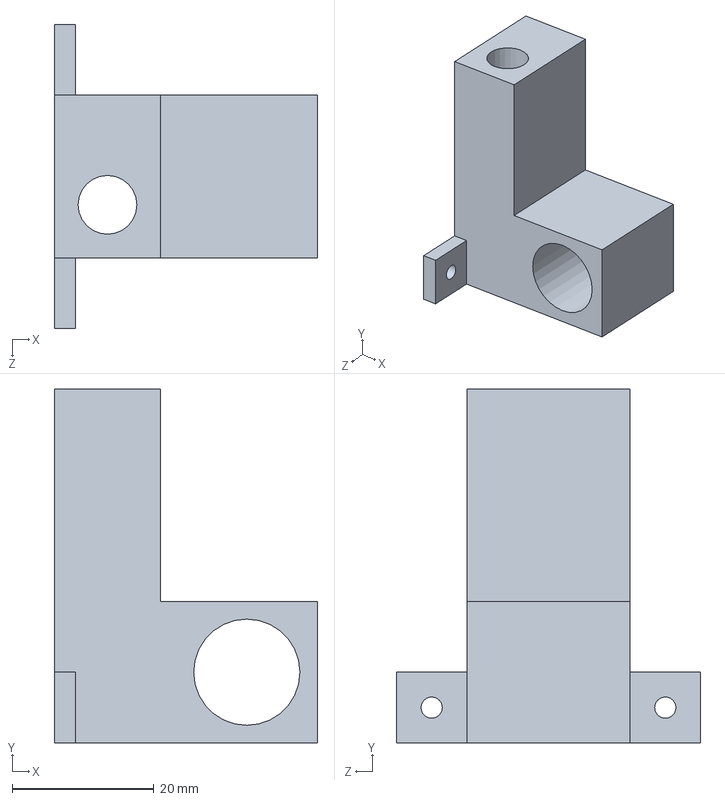
[picture p130: CAD file, 2019-03-12]
Prototype_Bottle_Mechanism/Holder_1_roller_long.SLDPRT
37.2 x 50.0 x 43.0 mm
