Apiquet/STI_Robotic_Competition_Mechanics/Drive_Base/Top_support_wheel.SLDPRT

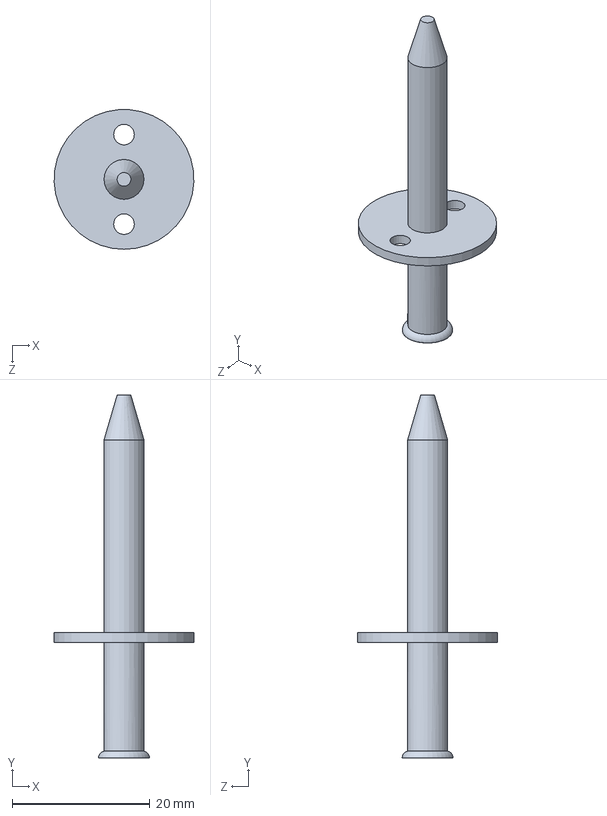
[picture p131: CAD file, 2019-03-19]
Drive_Base/Top_support_wheel.SLDPRT
20.3 x 52.7 x 20.3 mm
