Apiquet/STI_Robotic_Competition_Mechanics/Divers/Pole_Wood.SLDPRT

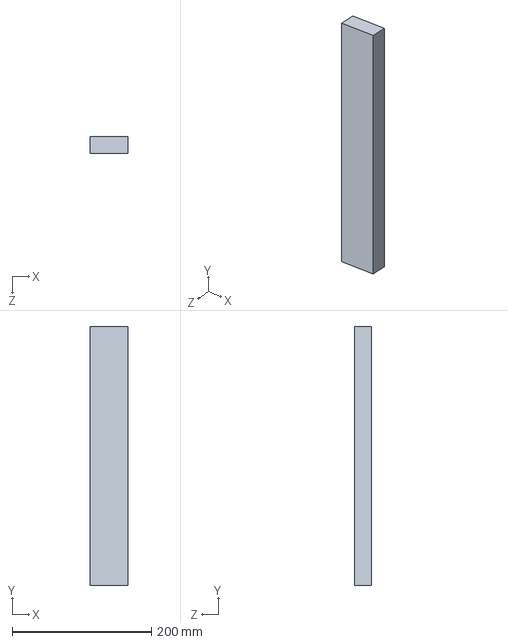
[picture p133: CAD file, 2019-04-23]
Divers/Pole_Wood.SLDPRT
54.0 x 372.2 x 24.5 mm
